fpiesik/ElektroCaster/docs/ext_ressources/circuits/piezoPreamps/Pokemon Ausmalbilder Kostenlos Malvorlagen Windowcolor zum Drucken-Dateien/ads_data_003/1356973211970626245.png

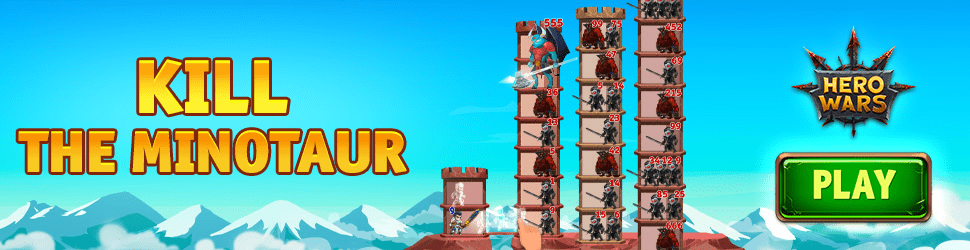
docs/ext_ressources/circuits/piezoPreamps/Pokemon Ausmalbilder Kostenlos Malvorlagen Windowcolor zum Drucken-Dateien/ads_data_003/1356973211970626245.png
