fpiesik/ElektroCaster/docs/UserInterface/DSC01511.JPG

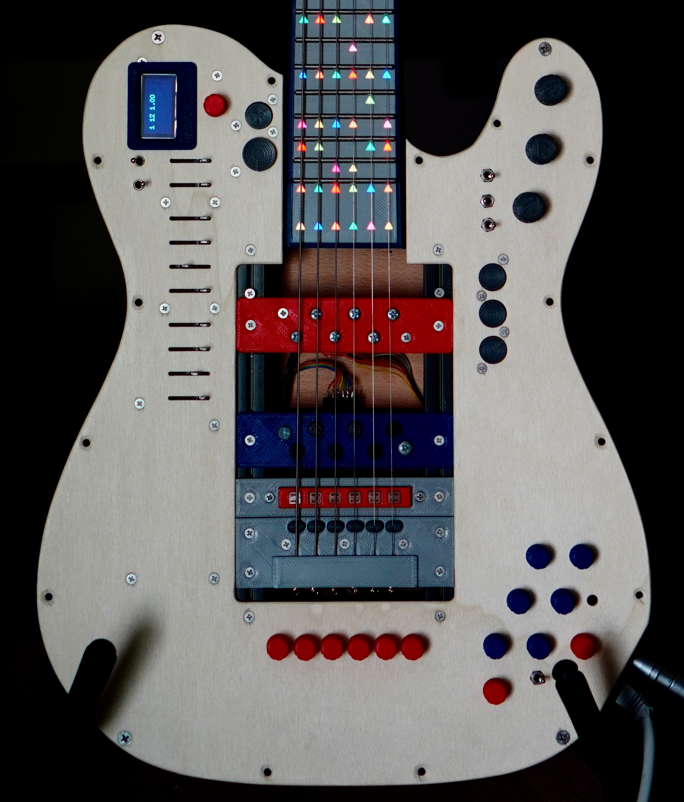
docs/UserInterface/DSC01511.JPG
