fpiesik/ElektroCaster/docs/ext_ressources/circuits/gk3.png

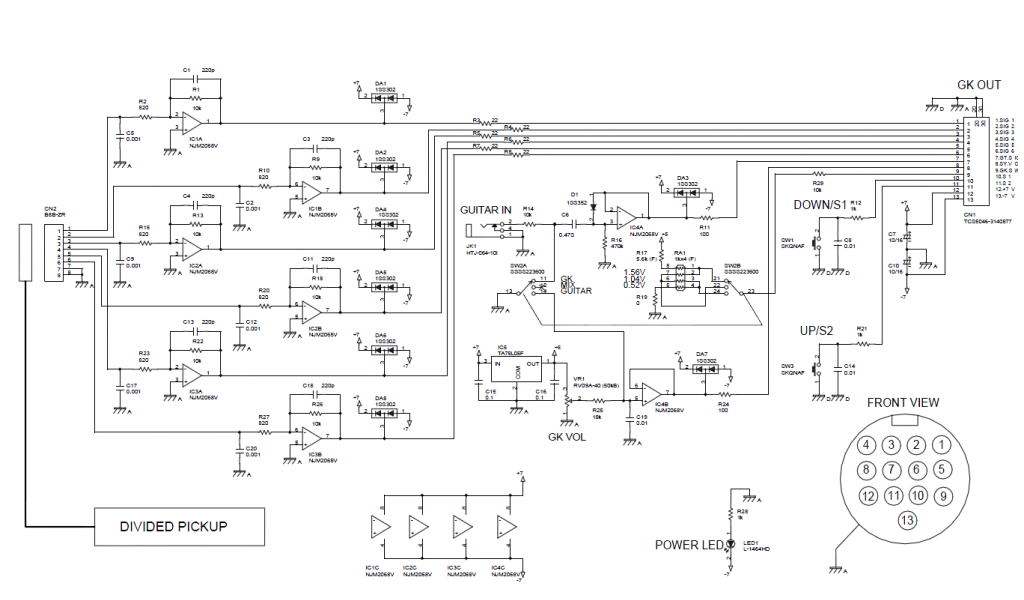
docs/ext_ressources/circuits/gk3.png
