fpiesik/ElektroCaster/docs/ext_ressources/circuits/gkCablePin.jpg

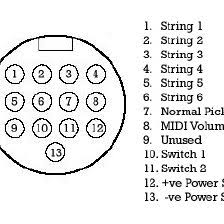
docs/ext_ressources/circuits/gkCablePin.jpg
