fpiesik/ElektroCaster/docs/ext_ressources/circuits/jfet-preamp.gif

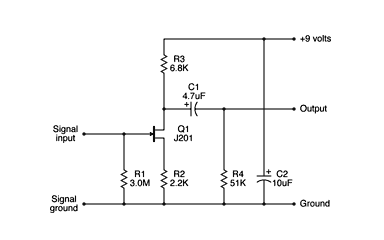
docs/ext_ressources/circuits/jfet-preamp.gif
