fpiesik/ElektroCaster/docs/ext_ressources/circuits/piezoPreamps/Pokemon Ausmalbilder Kostenlos Malvorlagen Windowcolor zum Drucken-Dateien/Ausmalbilder-Pokemon-Amphizel-300x236.jpg

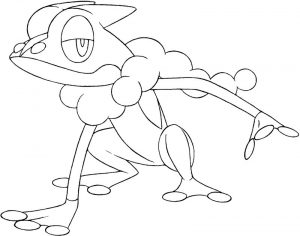
docs/ext_ressources/circuits/piezoPreamps/Pokemon Ausmalbilder Kostenlos Malvorlagen Windowcolor zum Drucken-Dateien/Ausmalbilder-Pokemon-Amphizel-300x236.jpg
