fpiesik/ElektroCaster/docs/ext_ressources/circuits/piezoPreamps/Pokemon Ausmalbilder Kostenlos Malvorlagen Windowcolor zum Drucken-Dateien/Ausmalbilder-Pokemon-Arceus-300x281.jpg

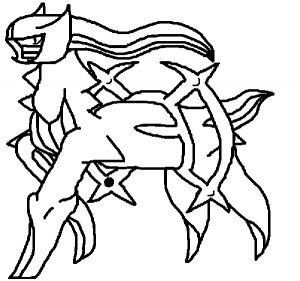
docs/ext_ressources/circuits/piezoPreamps/Pokemon Ausmalbilder Kostenlos Malvorlagen Windowcolor zum Drucken-Dateien/Ausmalbilder-Pokemon-Arceus-300x281.jpg
