fpiesik/ElektroCaster/docs/ext_ressources/circuits/piezoPreamps/Pokemon Ausmalbilder Kostenlos Malvorlagen Windowcolor zum Drucken-Dateien/Ausmalbilder-Pokemon-Ash.gif

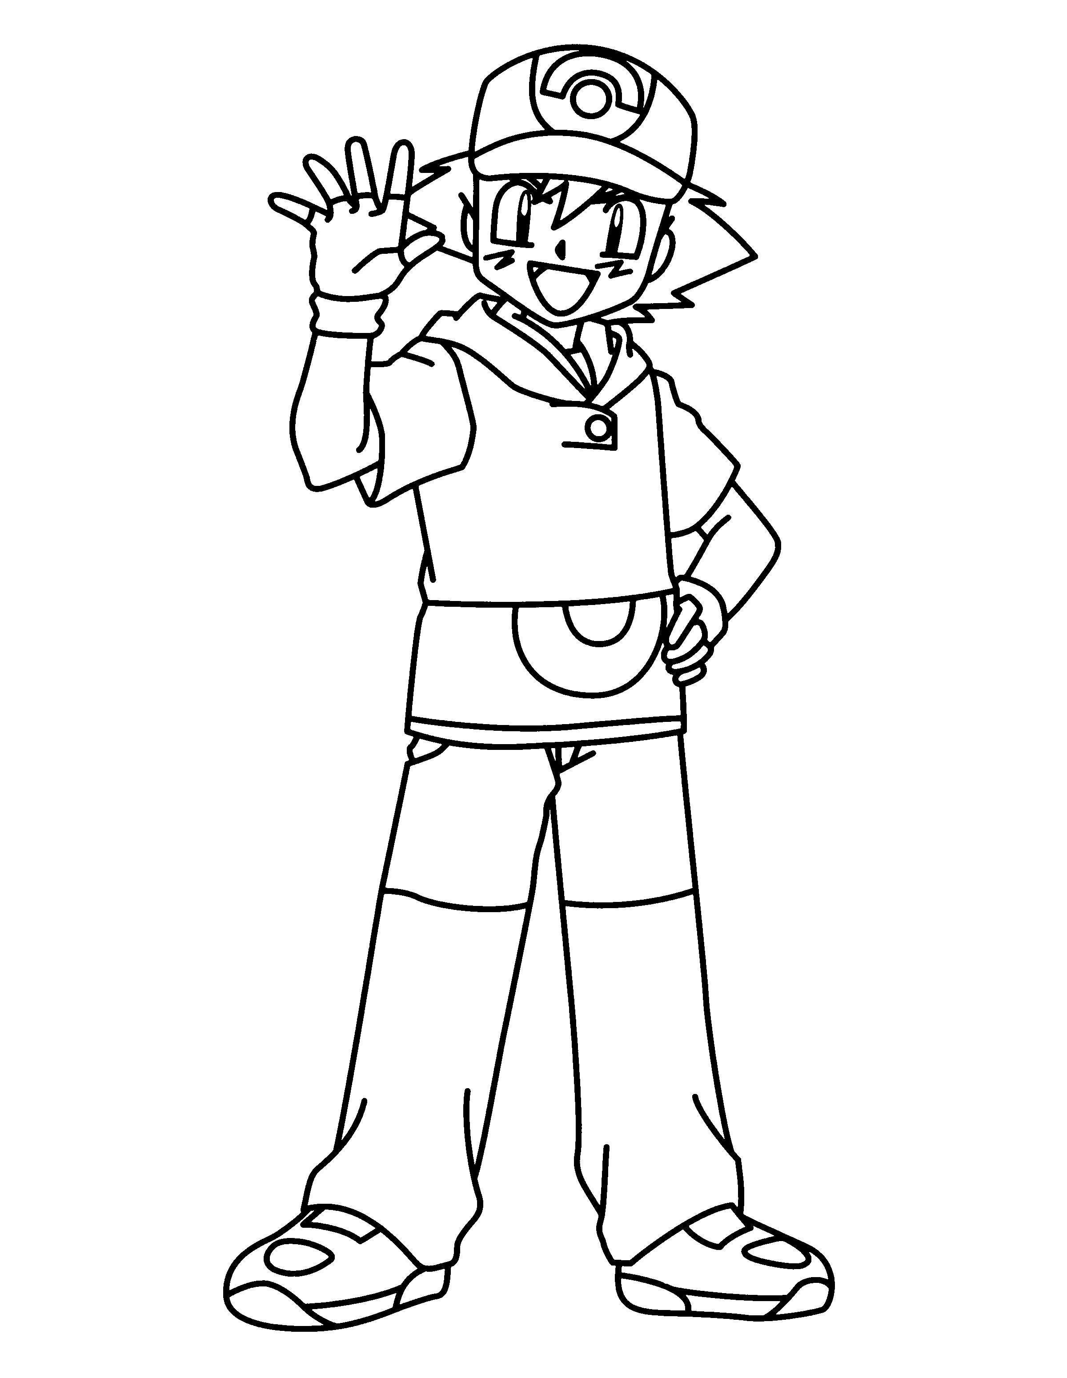
docs/ext_ressources/circuits/piezoPreamps/Pokemon Ausmalbilder Kostenlos Malvorlagen Windowcolor zum Drucken-Dateien/Ausmalbilder-Pokemon-Ash.gif
