fpiesik/ElektroCaster/docs/ext_ressources/circuits/piezoPreamps/Pokemon Ausmalbilder Kostenlos Malvorlagen Windowcolor zum Drucken-Dateien/Ausmalbilder-Pokemon-Ball.gif

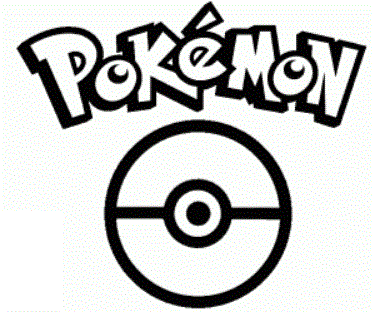
docs/ext_ressources/circuits/piezoPreamps/Pokemon Ausmalbilder Kostenlos Malvorlagen Windowcolor zum Drucken-Dateien/Ausmalbilder-Pokemon-Ball.gif
