fpiesik/ElektroCaster/docs/ext_ressources/circuits/piezoPreamps/prePiez.png

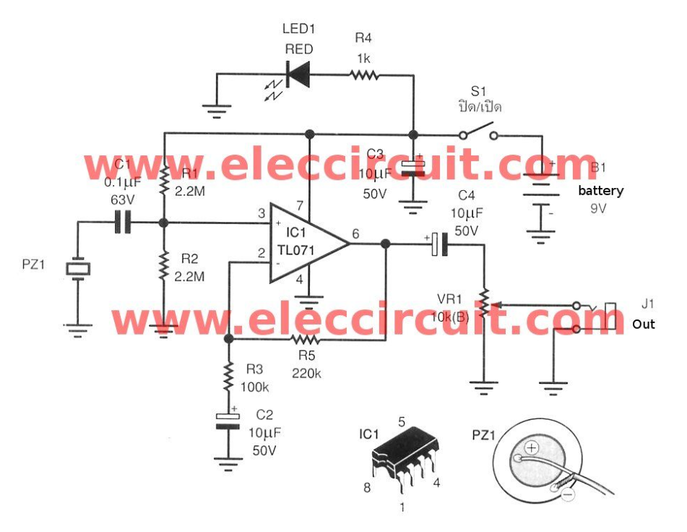
docs/ext_ressources/circuits/piezoPreamps/prePiez.png
