fpiesik/ElektroCaster/docs/ext_ressources/circuits/piezoPreamps/stack.png

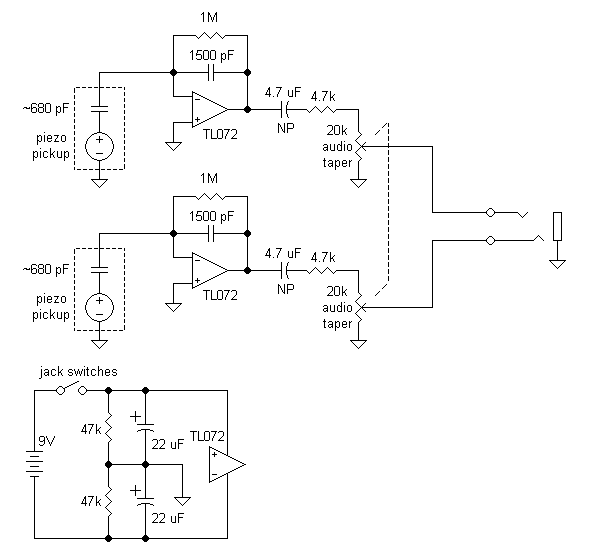
docs/ext_ressources/circuits/piezoPreamps/stack.png
