fpiesik/ElektroCaster/docs/ext_ressources/circuits/symmetricPower.jpg

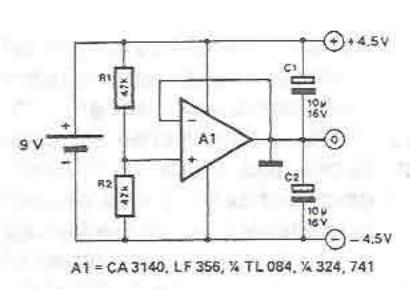
docs/ext_ressources/circuits/symmetricPower.jpg
