fpiesik/ElektroCaster/docs/ext_ressources/circuits/symmetricPower.png

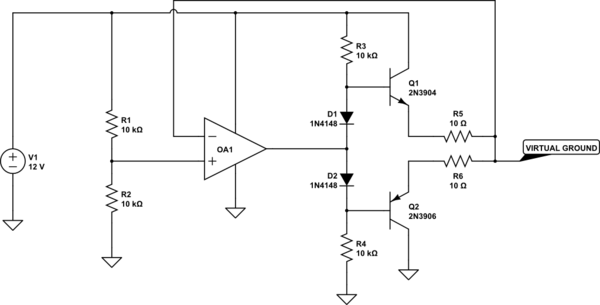
docs/ext_ressources/circuits/symmetricPower.png
