fpiesik/ElektroCaster/docs/UserInterface/PICT_20200703_101951.JPG

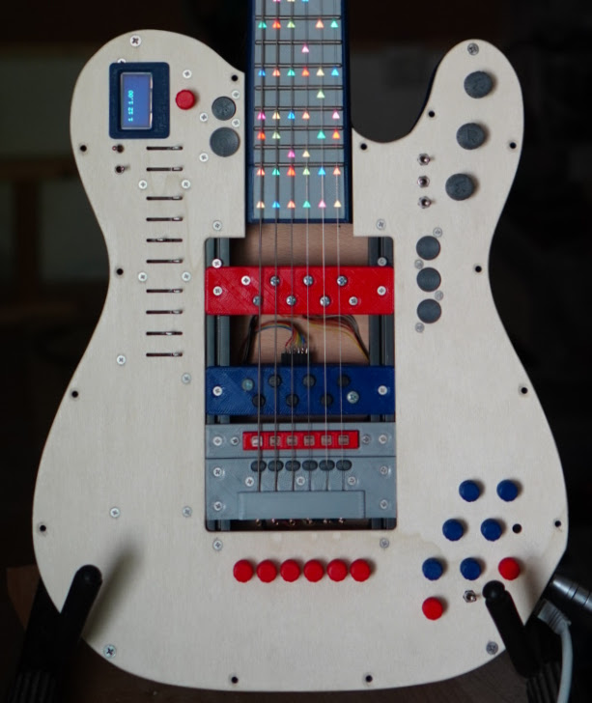
docs/UserInterface/PICT_20200703_101951.JPG
