fpiesik/ElektroCaster/mechanics/fretboard/fretConnect.stl

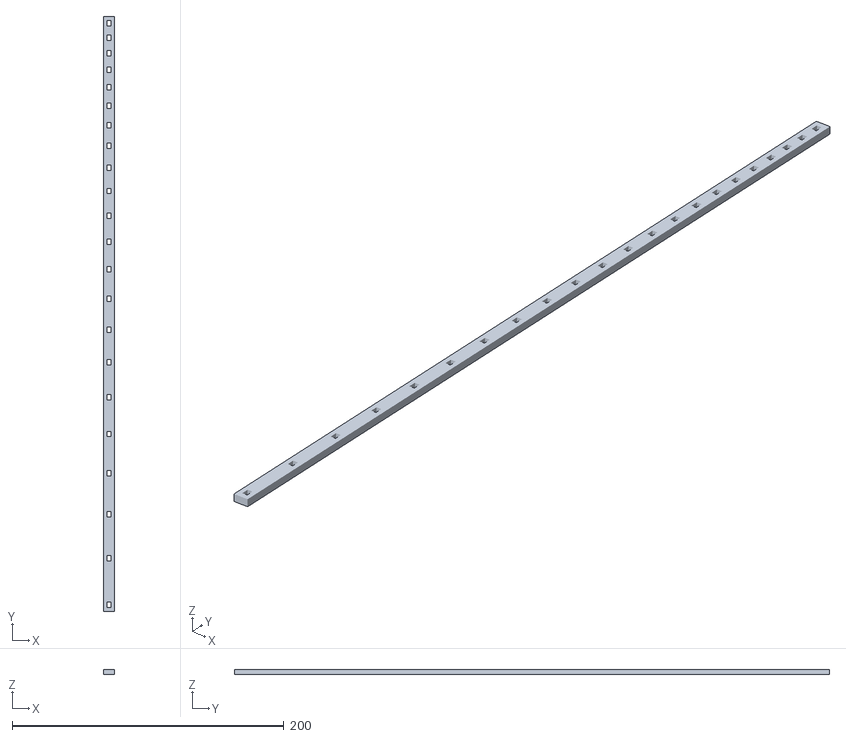
[picture p50: CAD file, 2022-02-02]
mechanics/fretboard/fretConnect.stl
8.00 x 437.8 x 4.00
