fpiesik/ElektroCaster/mechanics/knobs/knobs_joy.stl

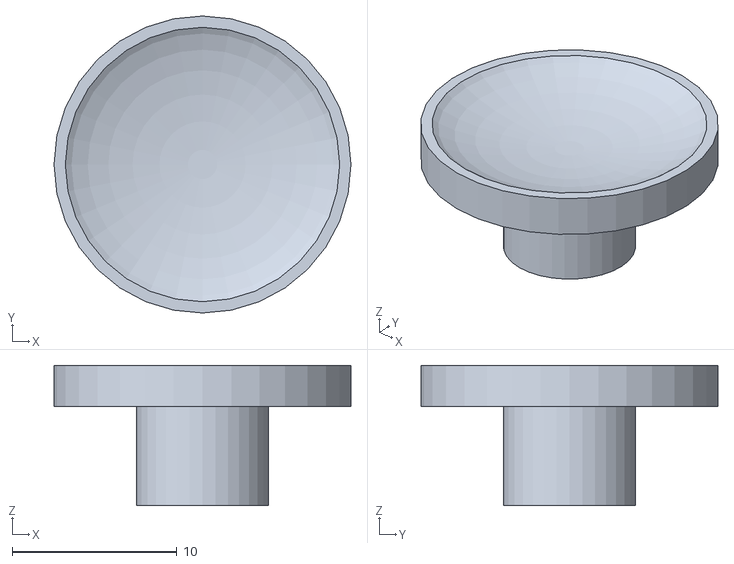
[picture p52: CAD file, 2020-10-20]
mechanics/knobs/knobs_joy.stl
18.0 x 18.0 x 8.50
