fpiesik/ElektroCaster/mechanics/neck/neck-over+side.stl

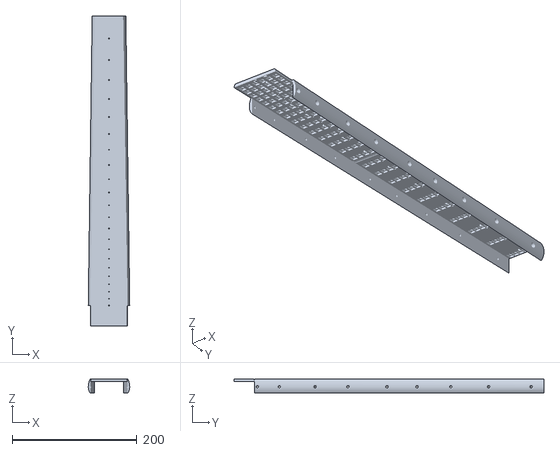
[picture p53: CAD file, 2022-02-02]
mechanics/neck/neck-over+side.stl
66.5 x 496.7 x 23.1
