fpiesik/ElektroCaster/mechanics/pickup(HB)/hexPickup-B.stl

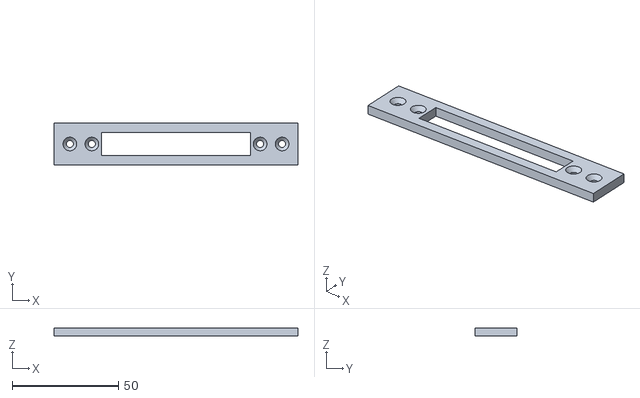
[picture p54: CAD file, 2020-10-20]
mechanics/pickup(HB)/hexPickup-B.stl
115.0 x 20.0 x 4.00
