fpiesik/ElektroCaster/mechanics/skeleton/slotBody2BackMntscad.stl

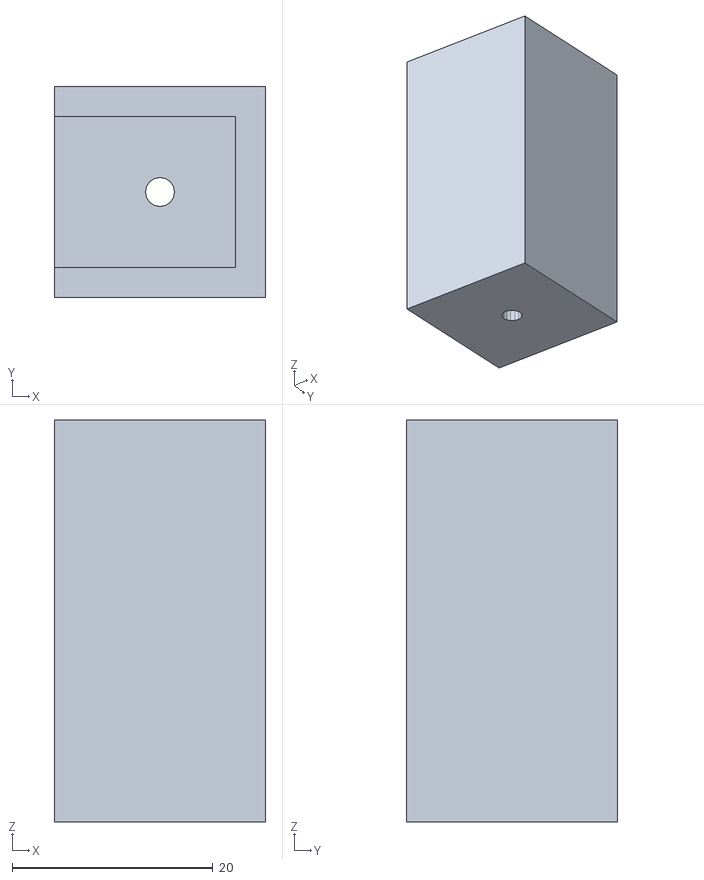
[picture p55: CAD file, 2020-10-20]
mechanics/skeleton/slotBody2BackMntscad.stl
21.0 x 21.0 x 40.0
