fpiesik/ElektroCaster/mechanics/body/bodyCont.stl

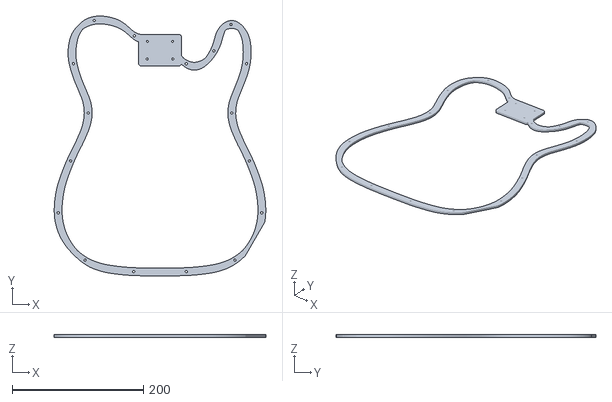
[picture p56: CAD file, 2020-10-20]
mechanics/body/bodyCont.stl
322.0 x 395.7 x 4.00
