fpiesik/ElektroCaster/mechanics/bridge/bridge-B (piezo).stl

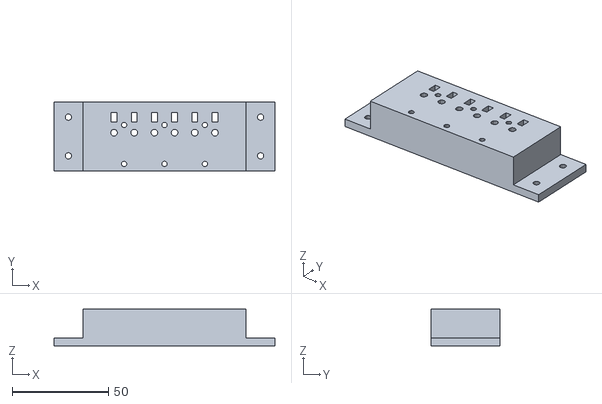
[picture p57: CAD file, 2022-02-02]
mechanics/bridge/bridge-B (piezo).stl
115.0 x 36.0 x 19.0
