fpiesik/ElektroCaster/mechanics/fretboard/fretboard.stl

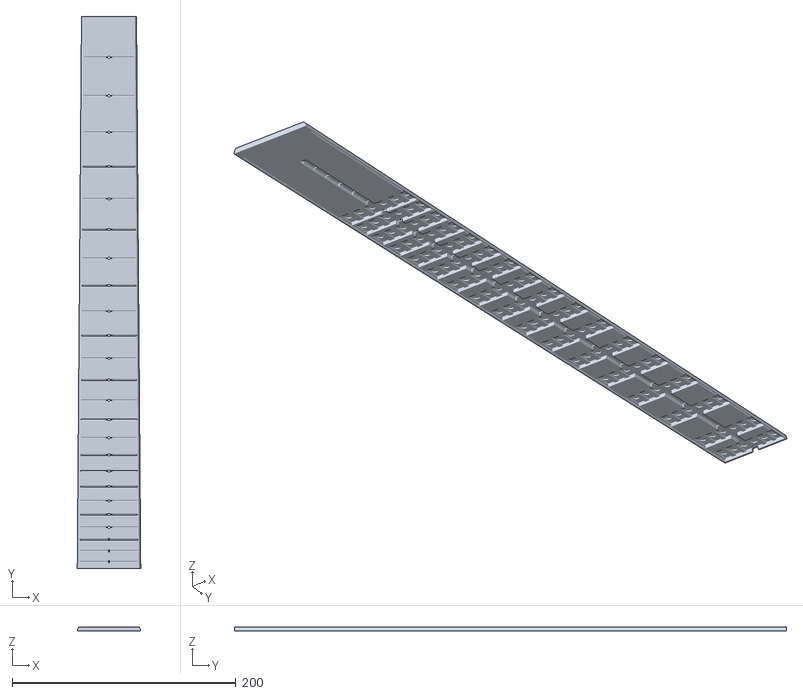
[picture p58: CAD file, 2020-10-20]
mechanics/fretboard/fretboard.stl
56.8 x 493.6 x 3.50
