fpiesik/ElektroCaster/mechanics/head/tuners.stl

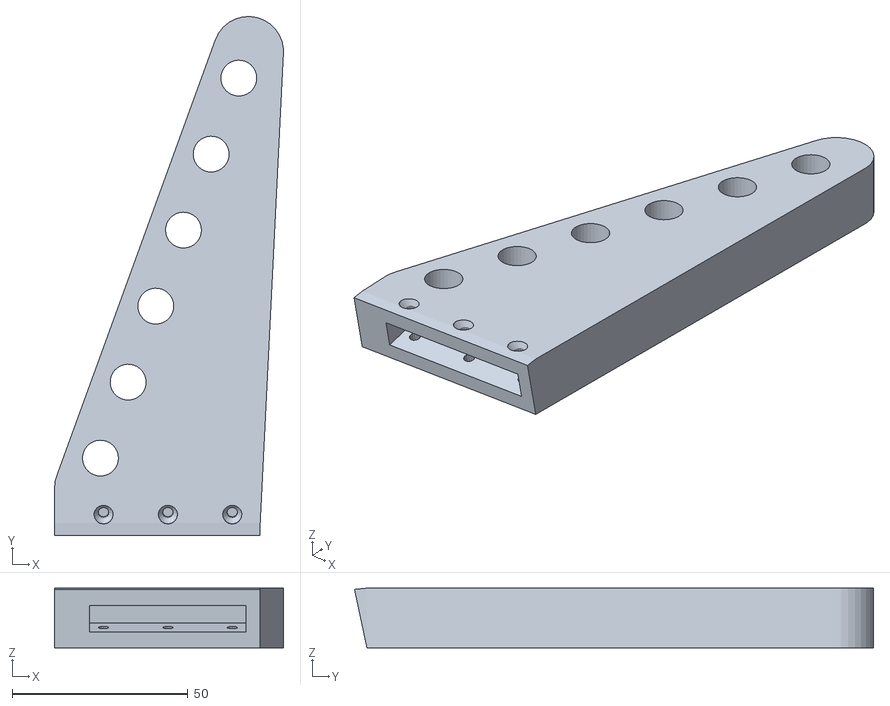
[picture p59: CAD file, 2020-10-20]
mechanics/head/tuners.stl
65.1 x 147.6 x 17.0
