fpiesik/ElektroCaster/mechanics/knobs/encKnob(ext).stl

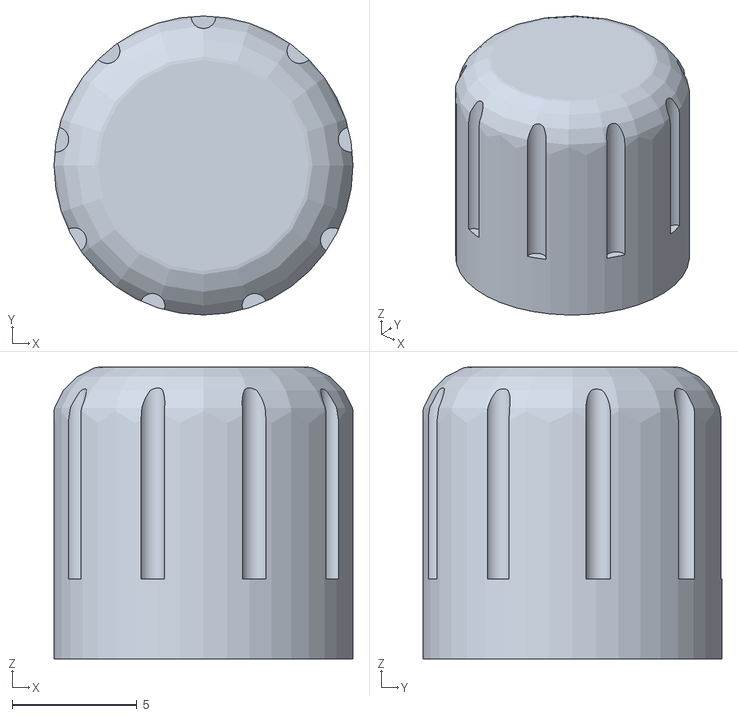
[picture p60: CAD file, 2020-10-20]
mechanics/knobs/encKnob(ext).stl
12.0 x 12.0 x 11.7
