fpiesik/ElektroCaster/mechanics/neck/neck-side.stl

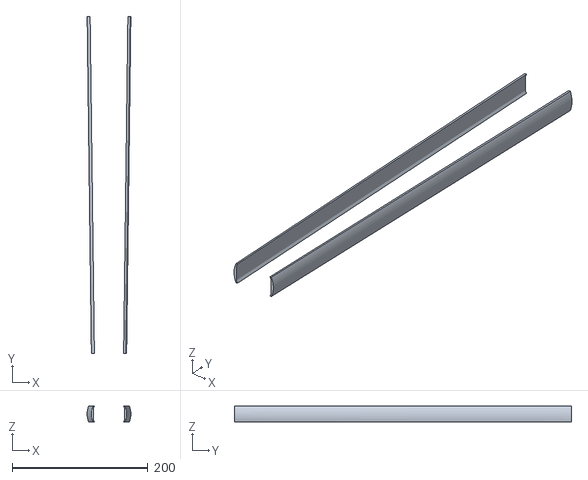
[picture p61: CAD file, 2020-10-20]
mechanics/neck/neck-side.stl
64.5 x 496.7 x 23.1
