fpiesik/ElektroCaster/mechanics/pickup(HB)/hexPickup-C.stl

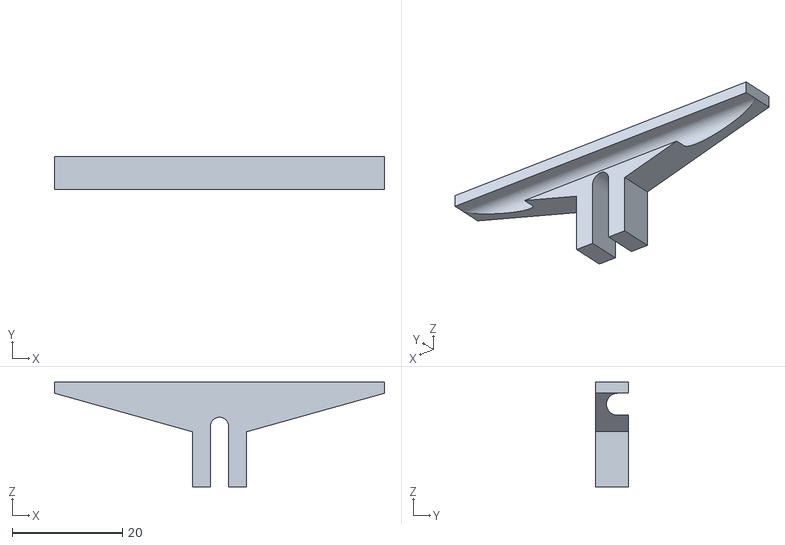
[picture p62: CAD file, 2020-10-20]
mechanics/pickup(HB)/hexPickup-C.stl
60.0 x 6.00 x 19.0
