fpiesik/ElektroCaster/docs/ext_ressources/nu_pickups/nu-master/cad_drawings/nu_multi/Nu_Multi_6_Routing_Template_Drawing.DXF

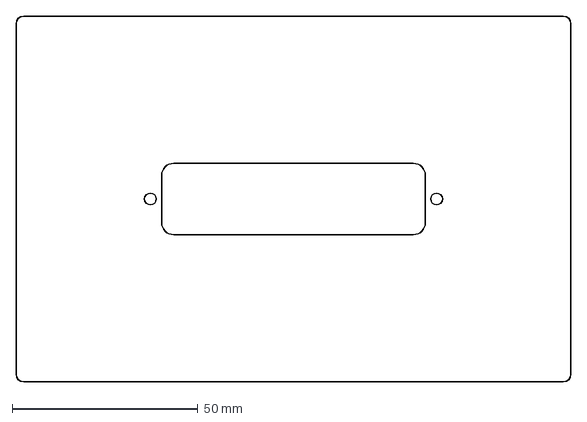
[picture p63: CAD file, 2022-02-02]
docs/ext_ressources/nu_pickups/nu-master/cad_drawings/nu_multi/Nu_Multi_6_Routing_Template_Drawing.DXF
149.2 x 98.4 mm
