fpiesik/ElektroCaster/mechanics/body/bodyConFilled.dxf

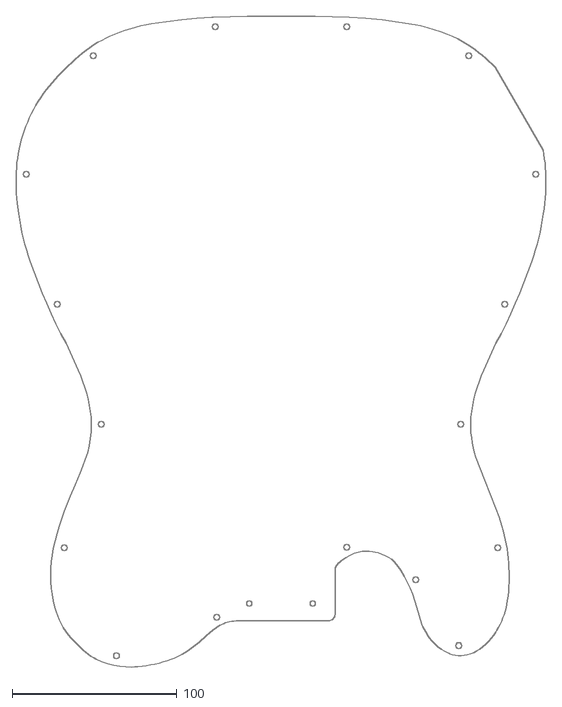
[picture p64: CAD file, 2020-10-20]
mechanics/body/bodyConFilled.dxf
322.0 x 395.7
