fpiesik/ElektroCaster/mechanics/bridge/bridge-A (piezo).stl

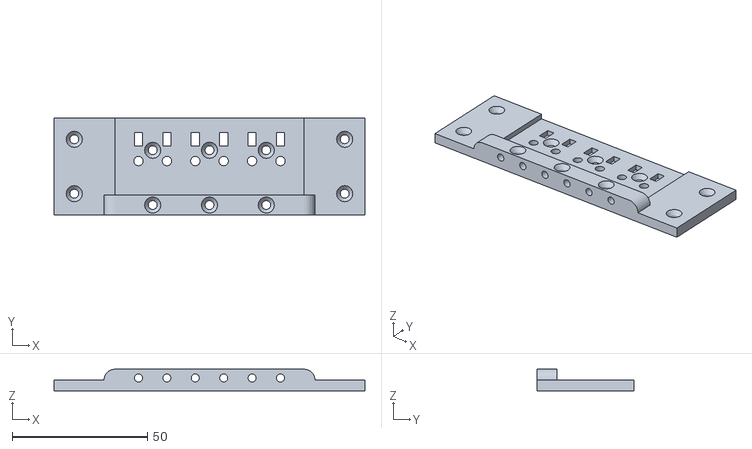
[picture p65: CAD file, 2022-02-02]
mechanics/bridge/bridge-A (piezo).stl
115.0 x 36.0 x 8.00
