fpiesik/ElektroCaster/mechanics/fretboard/overlay.stl

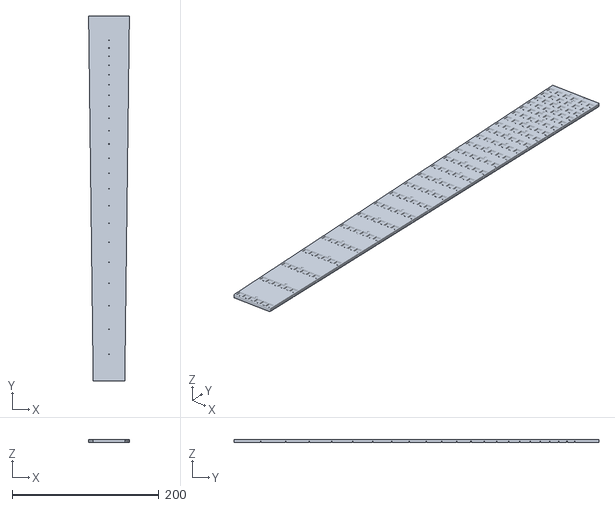
[picture p66: CAD file, 2020-10-20]
mechanics/fretboard/overlay.stl
55.4 x 496.7 x 3.50
