fpiesik/ElektroCaster/mechanics/kickup_mEbow/mcMag.stl

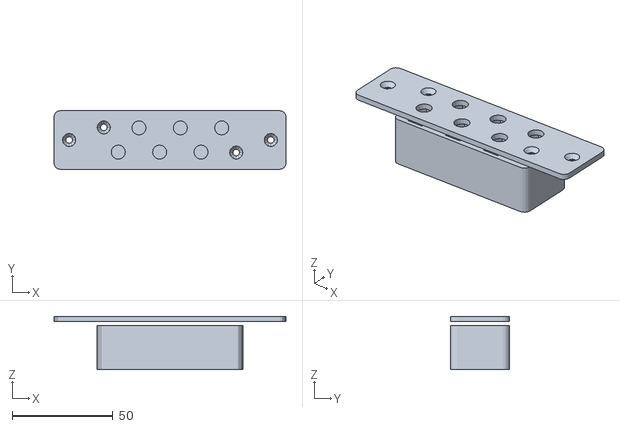
[picture p67: CAD file, 2020-10-20]
mechanics/kickup_mEbow/mcMag.stl
115.0 x 29.0 x 26.3
