fpiesik/ElektroCaster/mechanics/knobs/knobs_button.stl

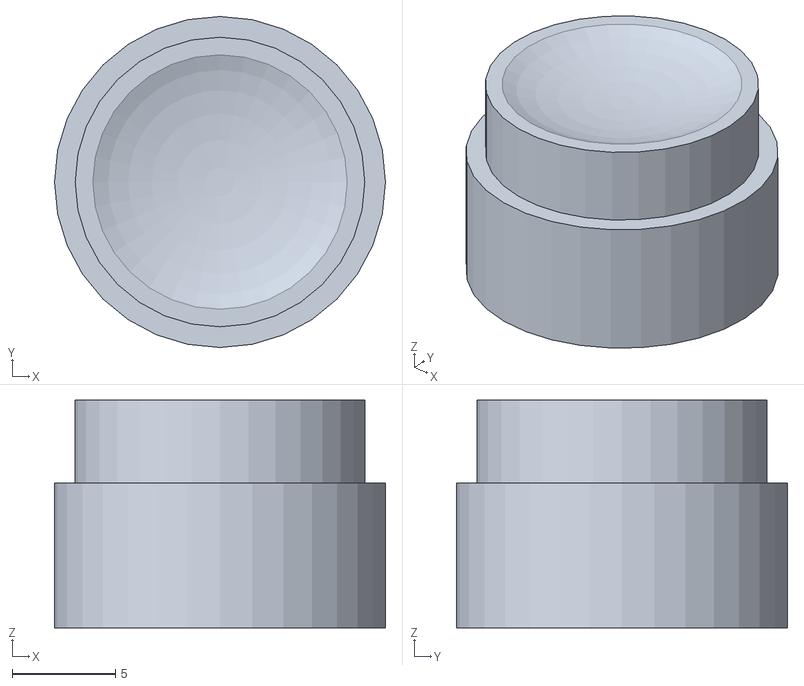
[picture p68: CAD file, 2020-10-20]
mechanics/knobs/knobs_button.stl
16.0 x 16.0 x 11.0
