fpiesik/ElektroCaster/mechanics/neck/neck-endB.stl

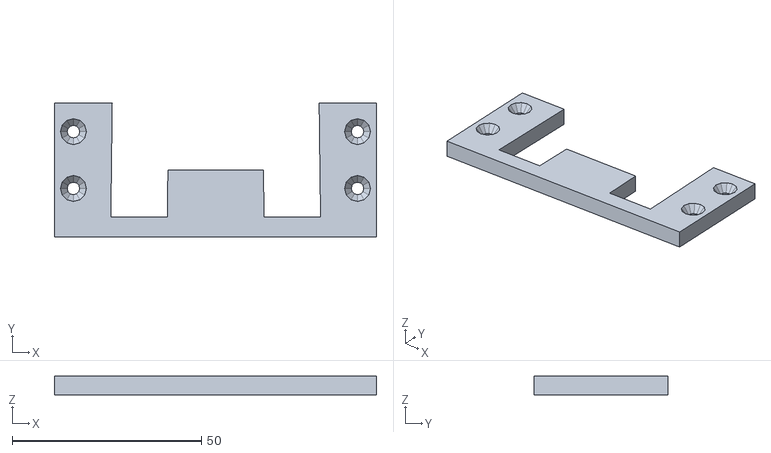
[picture p69: CAD file, 2020-10-20]
mechanics/neck/neck-endB.stl
85.0 x 35.2 x 5.00
