fpiesik/ElektroCaster/mechanics/pickup(HB)/hexPickup-A.stl

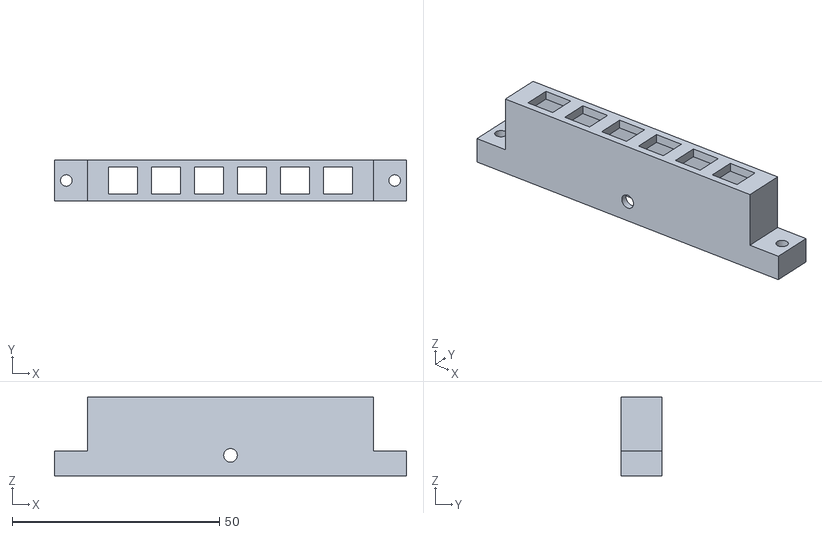
[picture p70: CAD file, 2020-10-20]
mechanics/pickup(HB)/hexPickup-A.stl
85.0 x 10.0 x 19.0
