fpiesik/ElektroCaster/mechanics/body/centerLine.dxf

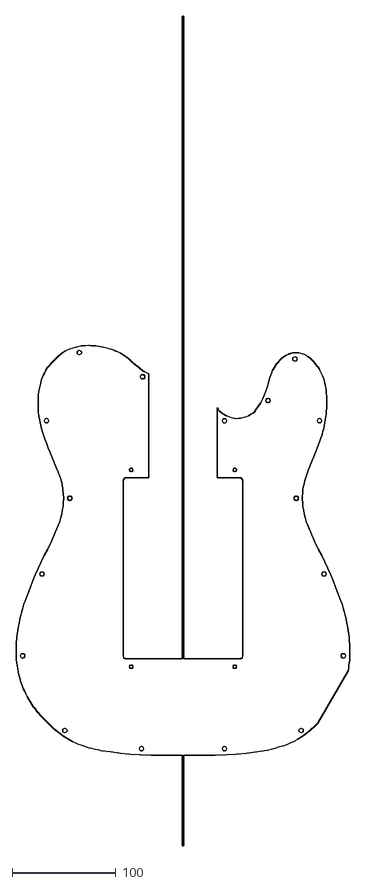
[picture p71: CAD file, 2020-10-20]
mechanics/body/centerLine.dxf
322.0 x 800.0
