fpiesik/ElektroCaster/mechanics/bridge/bridge-A.stl

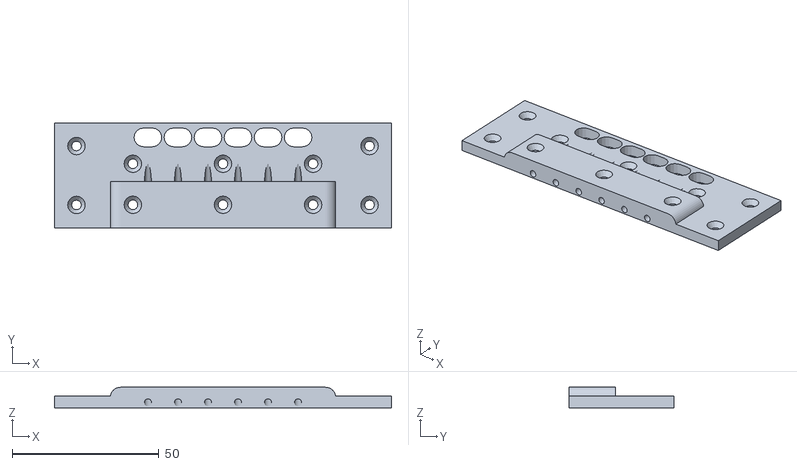
[picture p72: CAD file, 2021-02-15]
mechanics/bridge/bridge-A.stl
115.0 x 36.0 x 7.00
