fpiesik/ElektroCaster/mechanics/fretboard/contour.dxf

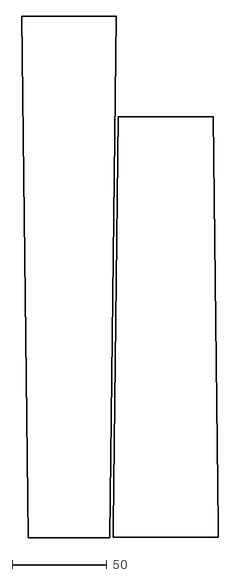
[picture p73: CAD file, 2020-10-20]
mechanics/fretboard/contour.dxf
103.7 x 275.0
