fpiesik/ElektroCaster/mechanics/kickup_mEbow/mcMag-top.stl

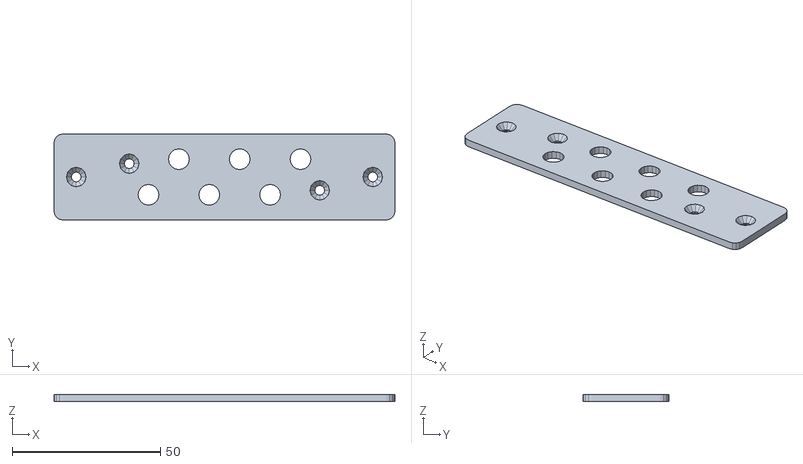
[picture p74: CAD file, 2020-10-20]
mechanics/kickup_mEbow/mcMag-top.stl
115.0 x 29.0 x 2.50
