fpiesik/ElektroCaster/mechanics/body/bodyTop(noKnobs).dxf

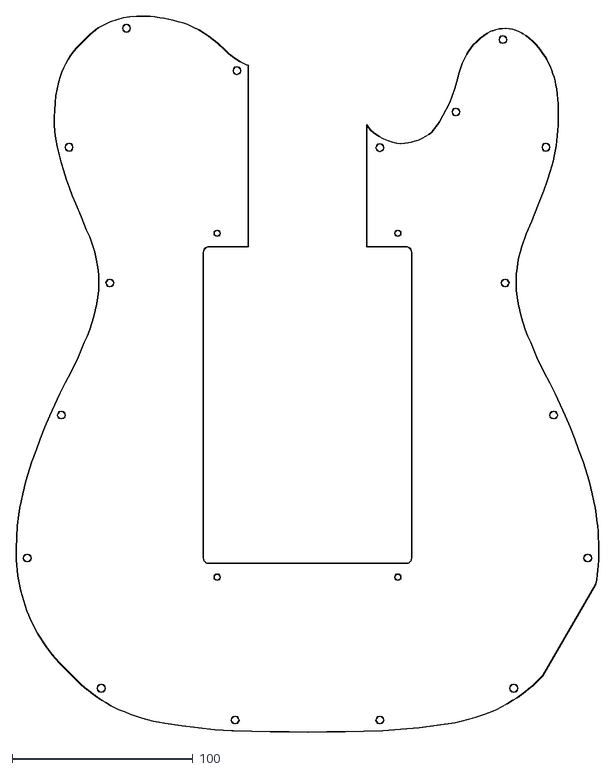
[picture p75: CAD file, 2020-10-20]
mechanics/body/bodyTop(noKnobs).dxf
322.0 x 395.7
