fpiesik/ElektroCaster/mechanics/bridge/bridge-C.stl

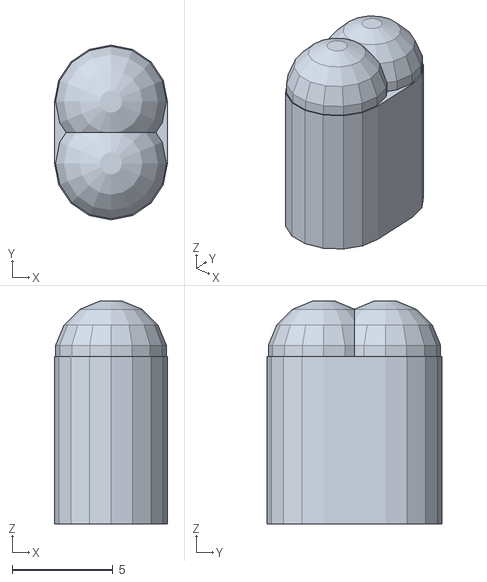
[picture p76: CAD file, 2021-02-15]
mechanics/bridge/bridge-C.stl
5.60 x 8.65 x 11.0
