fpiesik/ElektroCaster/mechanics/fretboard/traces.dxf

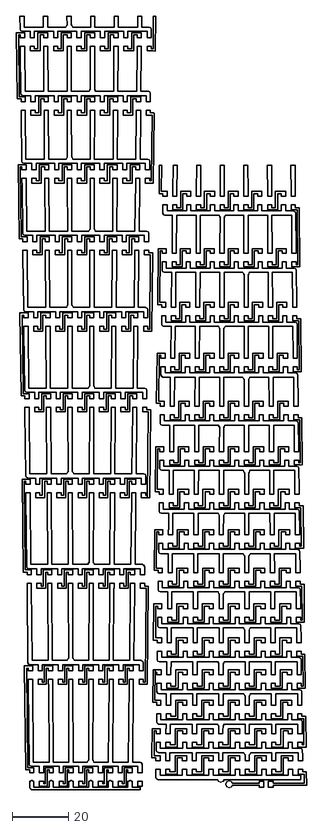
[picture p77: CAD file, 2020-10-20]
mechanics/fretboard/traces.dxf
103.2 x 275.0
