fpiesik/ElektroCaster/mechanics/kickup_mEbow/kickup.stl

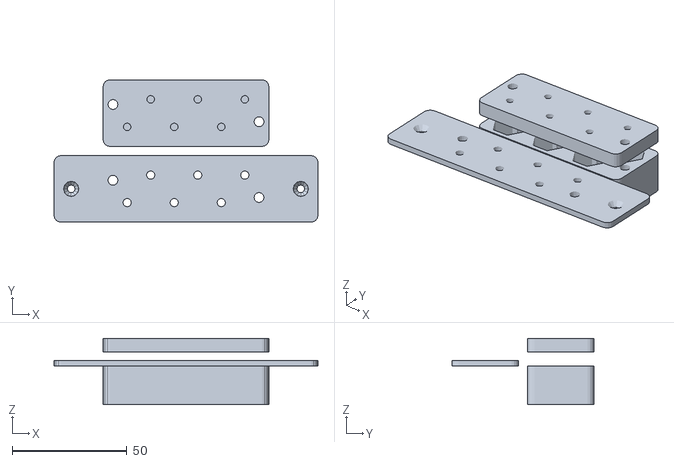
[picture p78: CAD file, 2020-10-20]
mechanics/kickup_mEbow/kickup.stl
115.0 x 62.0 x 28.8
