fpiesik/ElektroCaster/mechanics/neck/neck-mntSide.stl

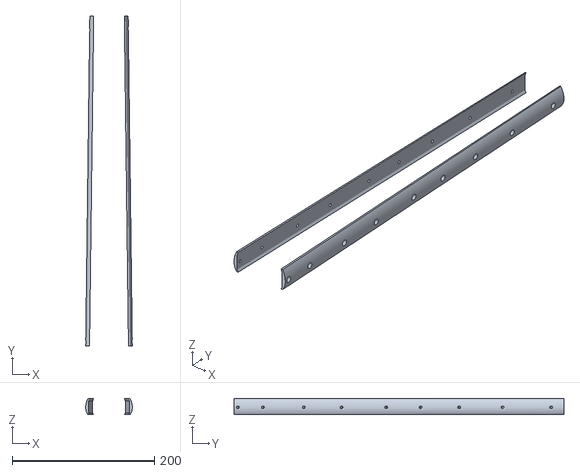
[picture p79: CAD file, 2020-10-20]
mechanics/neck/neck-mntSide.stl
65.7 x 464.0 x 23.1
