fpiesik/ElektroCaster/mechanics/body/body.stl

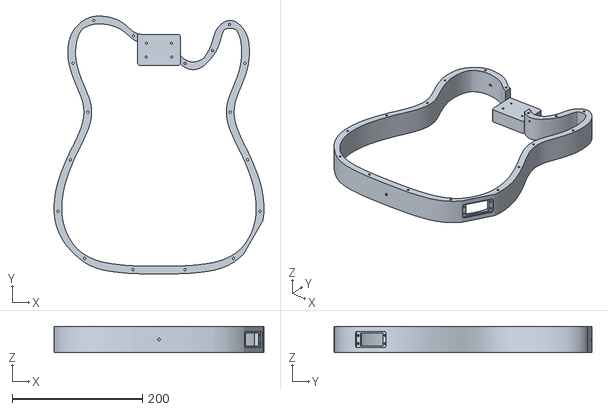
[picture p80: CAD file, 2020-10-20]
mechanics/body/body.stl
322.0 x 395.7 x 40.0
