fpiesik/ElektroCaster/mechanics/bridge/bridge-B.stl

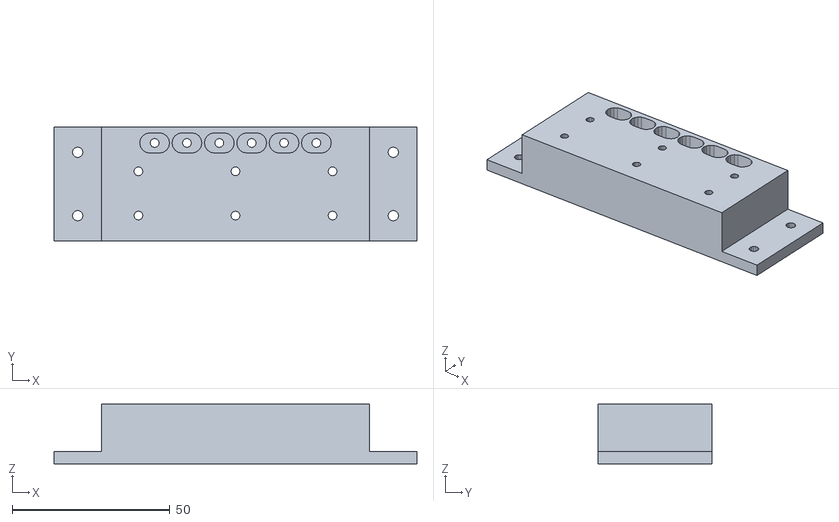
[picture p81: CAD file, 2021-02-15]
mechanics/bridge/bridge-B.stl
115.0 x 36.0 x 19.0
