fpiesik/ElektroCaster/mechanics/fretboard/ledStripe-drill.dxf

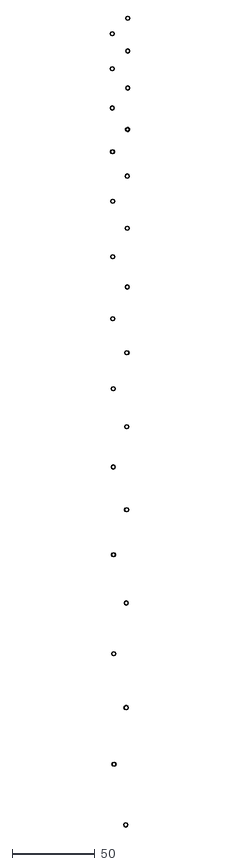
[picture p82: CAD file, 2020-10-20]
mechanics/fretboard/ledStripe-drill.dxf
11.9 x 490.0
