fpiesik/ElektroCaster/mechanics/neck/neck-over.stl

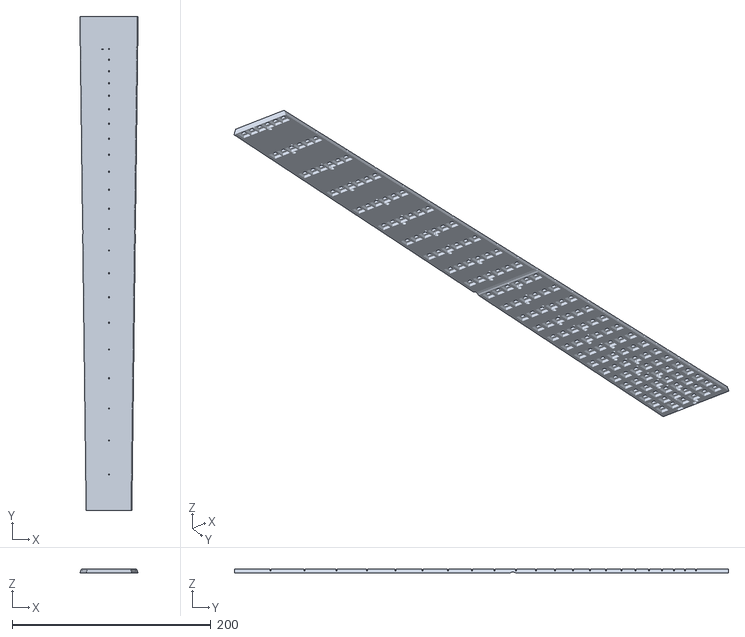
[picture p83: CAD file, 2020-10-20]
mechanics/neck/neck-over.stl
58.5 x 496.7 x 4.00
