fpiesik/ElektroCaster/mechanics/body/bodyContFilled2.stl

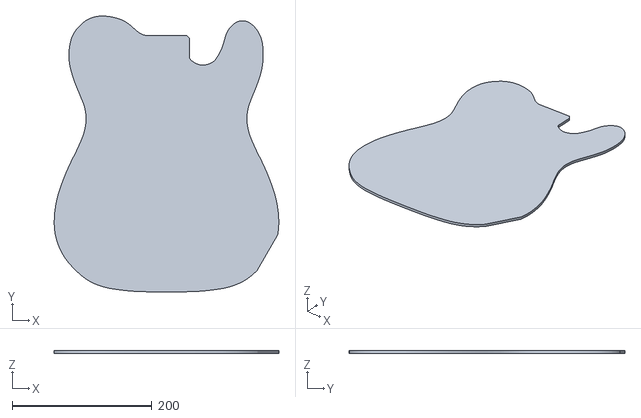
[picture p84: CAD file, 2020-10-20]
mechanics/body/bodyContFilled2.stl
322.0 x 395.7 x 4.00
