fpiesik/ElektroCaster/mechanics/fretboard/holes.dxf

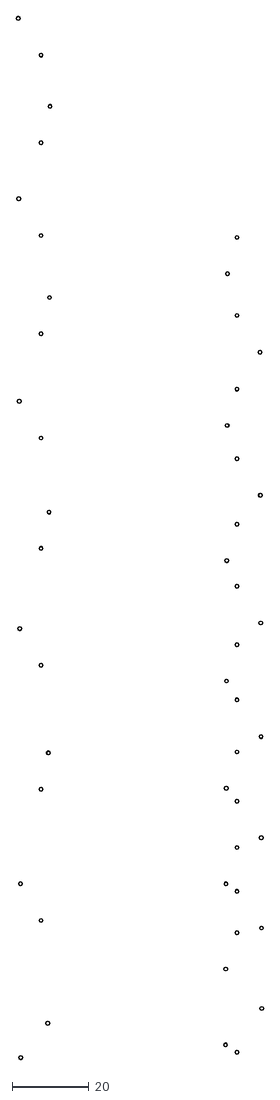
[picture p85: CAD file, 2020-10-20]
mechanics/fretboard/holes.dxf
64.4 x 271.5
