fpiesik/ElektroCaster/mechanics/neck/neck-sideB.stl

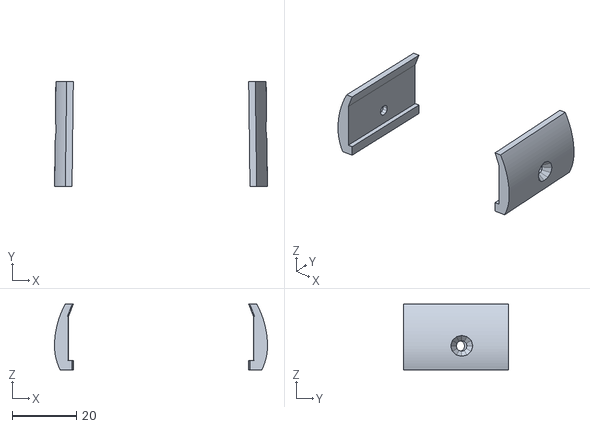
[picture p86: CAD file, 2020-10-20]
mechanics/neck/neck-sideB.stl
66.5 x 32.7 x 20.6
