fpiesik/ElektroCaster/mechanics/body/bodyContour.dxf

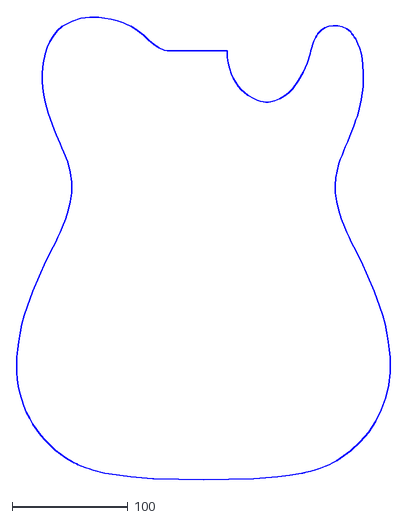
[picture p87: CAD file, 2019-02-02]
mechanics/body/bodyContour.dxf
323.4 x 400.7
