fpiesik/ElektroCaster/mechanics/fretboard/ledStripe.dxf

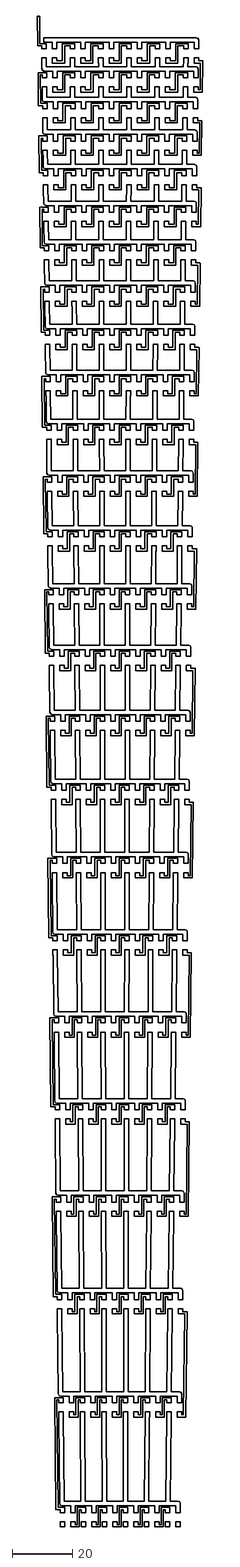
[picture p88: CAD file, 2020-10-20]
mechanics/fretboard/ledStripe.dxf
55.1 x 503.1
