fpiesik/ElektroCaster/mechanics/neck/neck-end.stl

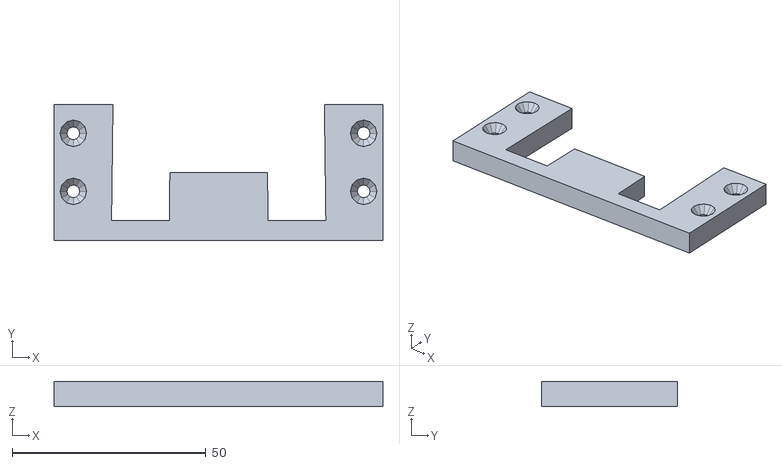
[picture p89: CAD file, 2020-10-20]
mechanics/neck/neck-end.stl
85.0 x 35.2 x 6.50
