fpiesik/ElektroCaster/mechanics/body/bodyTop.stl

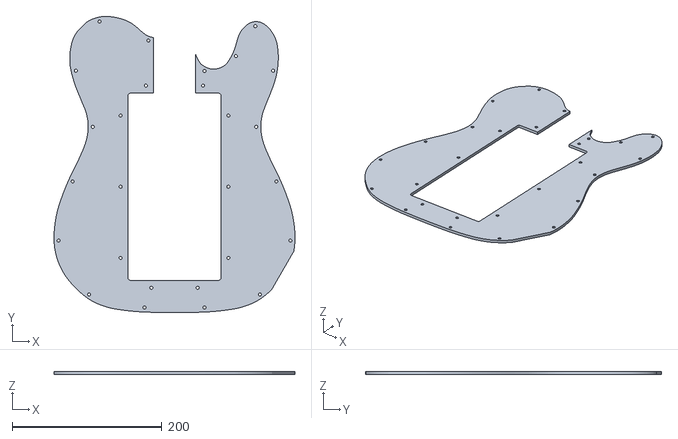
[picture p90: CAD file, 2019-02-02]
mechanics/body/bodyTop.stl
322.0 x 395.7 x 4.00
