fpiesik/ElektroCaster/mechanics/body/bodyContFilled.stl

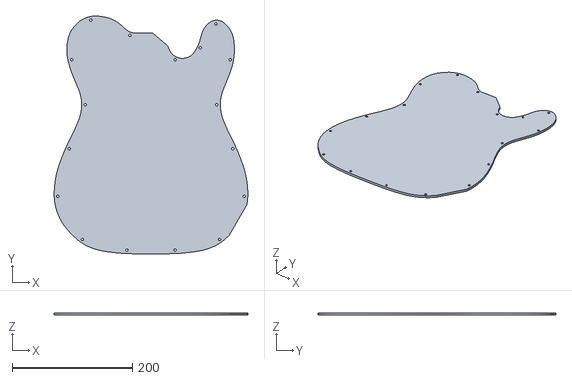
[picture p91: CAD file, 2019-02-02]
mechanics/body/bodyContFilled.stl
322.0 x 395.7 x 4.00
