fpiesik/ElektroCaster/electronics/hexPreamp(jfet)/case.scad

wO=40;
wthick=1;
wI=wO-wthick*2;

lO=90;
lI=lO-wthick*2;

h=20;


translate([0,0,h/2])cube([lO,wO,h],center=true);
