fpiesik/ElektroCaster/mechanics/body/inkbody.scad

// Module names are of the form poly_<inkscape-path-id>().
// As a result you can associate a polygon in this OpenSCAD program with the
//  corresponding SVG element in the Inkscape document by looking for 
//  the XML element with the attribute id="inkscape-path-id".

// Paths have their own variables so they can be imported and used 
//  in polygon(points) structures in other programs.
// The NN_points is the list of all polygon XY vertices. 
// There may be an NN_paths variable as well. If it exists then it 
//  defines the nested paths. Both must be used in the 
//  polygon(points, paths) variant of the command.

profile_scale = 25.4/90; //made in inkscape in mm

// helper functions to determine the X,Y dimensions of the profiles
function min_x(shape_points) = min([ for (x = shape_points) min(x[0])]);
function max_x(shape_points) = max([ for (x = shape_points) max(x[0])]);
function min_y(shape_points) = min([ for (x = shape_points) min(x[1])]);
function max_y(shape_points) = max([ for (x = shape_points) max(x[1])]);

height = 5;
width = 1.0;


path5353_0_points = [[290.911295,-521.752208],[300.775361,-534.505677],[309.902984,-547.742083],[318.278105,-561.429609],[325.884668,-575.536435],[332.706617,-590.030743],[338.727895,-604.880713],[343.932444,-620.054526],[348.304209,-635.520364],[354.002579,-655.936458],[360.678330,-676.060254],[363.301077,-682.612221],[366.363104,-688.966025],[369.853326,-695.099981],[373.760659,-700.992400],[378.552339,-706.731613],[383.900926,-711.822054],[389.740561,-716.249652],[396.005389,-720.000332],[402.629552,-723.060022],[409.547192,-725.414649],[416.692452,-727.050141],[423.999476,-727.952423],[431.402407,-728.107425],[438.835386,-727.501071],[446.232557,-726.119291],[453.528062,-723.948010],[460.656045,-720.973156],[467.550649,-717.180655],[474.146016,-712.556436],[480.376288,-707.086425],[484.929070,-701.778080],[489.164658,-696.225857],[493.073164,-690.443682],[496.644697,-684.445477],[500.639438,-676.880058],[504.274553,-669.153911],[507.545772,-661.279698],[510.448830,-653.270080],[512.979458,-645.137720],[515.133388,-636.895279],[516.906355,-628.555417],[518.294089,-620.130798],[519.724523,-608.899201],[520.850473,-597.647914],[521.672387,-586.382908],[522.190714,-575.110157],[522.405902,-563.835635],[522.318400,-552.565314],[521.928657,-541.305167],[521.237121,-530.061167],[520.244240,-518.839288],[518.950463,-507.645503],[517.356239,-496.485785],[515.462017,-485.366106],[513.268244,-474.292440],[510.775370,-463.270761],[507.983843,-452.307040],[504.894111,-441.407252]];
path5353_1_points = [[463.819263,-332.460017],[452.676031,-304.940580],[442.610874,-277.016939]];
path5353_2_points = [[447.012506,686.324879],[455.979492,680.365260],[464.730909,674.163900],[473.263284,667.726789],[481.573146,661.059921],[489.657020,654.169289],[497.511435,647.060884],[505.132917,639.740700],[512.517994,632.214728],[519.663193,624.488961],[526.565040,616.569392],[533.220064,608.462013],[539.624792,600.172816],[545.775749,591.707795],[551.669465,583.072940],[557.302465,574.274246],[562.671278,565.317703],[567.772430,556.209306],[572.602448,546.955045],[577.157860,537.560915],[581.435193,528.032906],[585.430974,518.377012],[589.141731,508.599224],[592.563989,498.705537],[595.694278,488.701941],[598.529123,478.594429],[601.065052,468.388994],[603.298592,458.091629],[605.226271,447.708325],[606.844615,437.245075],[608.150152,426.707872],[609.139408,416.102708],[609.808912,405.435576]];
path5353_3_points = [[442.614947,-277.016939],[439.226475,-265.396530],[436.367518,-253.656044],[434.040351,-241.813180],[432.247249,-229.885640],[430.990487,-217.891123],[430.272341,-205.847329],[430.095087,-193.771958],[430.460999,-181.682709]];
path5353_4_points = [[430.460999,-181.684023],[432.269928,-167.109492],[434.683009,-152.640034],[437.695241,-138.293720],[441.301623,-124.088619],[445.497157,-110.042802],[450.276840,-96.174337],[455.635674,-82.501296],[461.568658,-69.041747]];
path5353_5_points = [[461.568658,-69.041747],[475.638714,-36.643527],[490.719059,-4.692912]];
path5353_6_points = [[575.868423,190.747218],[566.973642,165.602070],[557.572761,140.646458],[547.668989,115.887775],[537.265535,91.333416],[526.365607,66.990774],[514.972413,42.867242],[503.089161,18.970216],[490.719059,-4.692912]];
path5353_7_points = [[604.079539,305.735709],[601.887231,291.068939],[599.310115,276.471243],[596.350011,261.949971],[593.008741,247.512472],[589.288126,233.166097],[585.189987,218.918196],[580.716146,204.776120],[575.868423,190.747218]];
path5353_8_points = [[609.808912,405.435576],[610.153109,392.932293],[610.193740,380.429866],[609.931107,367.933696],[609.365511,355.449183],[608.497255,342.981727],[607.326639,330.536729],[605.853967,318.119589],[604.079539,305.735709]];
path5353_9_points = [[334.803996,731.830129],[350.719196,727.624021],[366.474044,722.879552],[382.054599,717.601194],[397.446920,711.793416]];
path5353_10_points = [[163.557970,752.460102],[203.253864,749.737554],[242.841896,745.850708],[282.295883,740.802557],[321.589642,734.596092]];
path5353_11_points = [[-162.047715,752.511336],[-121.354457,753.704430],[-80.654675,754.554836],[-39.950567,755.062564],[0.755669,755.227625],[41.461838,755.050030],[82.165743,754.529790],[122.865186,753.666915],[163.557970,752.461416]];
path5353_12_points = [[-310.156338,736.525501],[-274.079401,741.952427],[-237.873087,746.404607],[-201.557433,749.879504],[-165.152478,752.374581]];
path5353_13_points = [[-410.189618,706.525935],[-397.849406,711.636849],[-385.371848,716.403070],[-372.764285,720.821985],[-360.034056,724.890984]];
path5353_14_points = [[-609.847492,404.626609],[-609.145077,416.045730],[-608.076903,427.390767],[-606.647415,438.654551],[-604.861060,449.829913],[-602.722286,460.909684],[-600.235538,471.886696],[-597.405265,482.753781],[-594.235913,493.503770],[-590.731929,504.129495],[-586.897760,514.623787],[-582.737852,524.979477],[-578.256653,535.189397],[-573.458610,545.246379],[-568.348169,555.143254],[-562.929778,564.872853],[-557.207883,574.428008],[-551.186931,583.801551],[-544.871370,592.986312],[-538.265645,601.975125],[-531.374205,610.760818],[-524.201496,619.336226],[-516.751964,627.694178],[-509.030057,635.827507],[-501.040222,643.729043],[-492.786906,651.391619],[-484.274555,658.808065],[-475.507616,665.971214],[-466.490537,672.873897],[-457.227764,679.508945],[-447.723744,685.869190],[-437.982924,691.947463],[-428.009751,697.736596]];
path5353_15_points = [[-604.079890,305.736365],[-607.308318,330.335473],[-609.347027,355.045028],[-610.193740,379.822813],[-609.846178,404.626609]];
path5353_16_points = [[-575.873897,190.747744],[-580.720662,204.776649],[-585.193682,218.918727],[-589.291113,233.166628],[-593.011111,247.513002],[-596.351833,261.950500],[-599.311432,276.471771],[-601.888066,291.069465],[-604.079890,305.736234]];
path5353_17_points = [[-490.719541,-4.692387],[-503.090962,18.970310],[-514.975393,42.867027],[-526.369597,66.990372],[-537.270337,91.332951],[-547.674374,115.887371],[-557.578471,140.646239],[-566.979392,165.602161],[-575.873897,190.747744]];
path5353_18_points = [[-490.719541,-4.692387],[-475.641003,-36.643000],[-461.572950,-69.041209]];
path5353_19_points = [[-461.574133,-69.041209],[-455.639842,-82.500381],[-450.280041,-96.173230],[-445.499722,-110.041623],[-441.303879,-124.087430],[-437.697508,-138.292521],[-434.685601,-152.638764],[-432.273154,-167.108029],[-430.465159,-181.682184]];
path5353_20_points = [[-430.465159,-181.683498],[-430.101674,-198.743118],[-430.818231,-215.741474],[-432.604835,-232.629505],[-435.451496,-249.358149],[-439.348220,-265.878343],[-444.285014,-282.141024],[-450.251885,-298.097132],[-457.238842,-313.697604]];
path5353_21_points = [[-457.238842,-313.697604],[-468.639113,-342.226877],[-480.702958,-370.488010]];
path5353_22_points = [[-506.993336,-441.954192],[-501.102181,-423.846491],[-494.754442,-405.893944],[-487.953556,-388.104808],[-480.702958,-370.487340]];
path5353_23_points = [[-524.202343,-512.003328],[-520.743489,-494.295256],[-516.720252,-476.708947],[-512.135808,-459.257705],[-506.993336,-441.954835]];
path5353_24_points = [[-517.498347,-635.971352],[-520.922213,-620.703407],[-523.610097,-605.318344],[-525.560603,-589.842118],[-526.772337,-574.300685],[-527.243904,-558.720001],[-526.973910,-543.126022],[-525.960959,-527.544704],[-524.203657,-512.002001]];
path5353_25_points = [[-478.294186,-710.270929],[-485.120893,-702.090254],[-491.423711,-693.543079],[-497.189417,-684.654543],[-502.404783,-675.449786],[-507.056585,-665.953949],[-511.131597,-656.192170],[-514.616593,-646.189592],[-517.498347,-635.971352]];
path5353_26_points = [[-454.868692,-729.202399],[-461.132848,-724.978680],[-467.135009,-720.407559],[-472.860386,-715.500991],[-478.294186,-710.270929]];
path5353_27_points = [[-342.452751,-754.276528],[-349.812296,-754.903018],[-357.169505,-755.227625],[-371.840789,-754.979250],[-386.394347,-753.547516],[-400.757921,-750.948535],[-414.859254,-747.198420],[-428.626091,-742.313284],[-441.986174,-736.309239],[-448.491103,-732.892662],[-454.867247,-729.202399]];
path5353_28_points = [[-262.119618,-736.766031],[-271.874971,-740.103665],[-281.728749,-743.116636],[-291.672640,-745.803159],[-301.698327,-748.161446],[-311.797497,-750.189713],[-321.961834,-751.886173],[-332.183023,-753.249040],[-342.452751,-754.276528]];
path5353_29_points = [[-262.118304,-736.767345],[-255.174530,-734.053201],[-248.547483,-731.149184],[-236.171327,-724.843489],[-224.845344,-717.994172],[-214.425041,-710.745147],[-204.765925,-703.240326],[-195.723505,-695.623625],[-178.910780,-680.630229],[-170.851490,-673.541363],[-162.830924,-666.916269],[-154.704591,-660.898860],[-146.327998,-655.633049],[-137.556652,-651.262751],[-132.977793,-649.458392],[-128.246061,-647.931878],[-123.343394,-646.701199],[-118.251732,-645.784344],[-112.953012,-645.199302],[-107.429172,-644.964063],[13.208202,-644.964063],[77.082179,-644.964063],[77.320197,-634.486266],[78.019436,-624.361856],[79.157676,-614.589381],[80.712698,-605.167390],[82.662281,-596.094431],[84.984204,-587.369052],[87.656248,-578.989803],[90.656192,-570.955231],[93.961815,-563.263885],[97.550899,-555.914314],[101.401222,-548.905067],[105.490564,-542.234691],[109.796705,-535.901736],[114.297425,-529.904750],[118.970503,-524.242281],[123.793720,-518.912878],[128.744854,-513.915089],[133.801687,-509.247464],[144.143564,-500.896896],[154.641589,-493.849562],[165.118000,-488.093852],[175.395035,-483.618152],[185.294933,-480.410852],[194.639931,-478.460340],[203.252267,-477.755003],[211.467846,-478.019691],[218.977927,-478.954548],[225.986509,-480.441340],[232.697590,-482.361832]];
path5353_30_points = [[232.697590,-482.361307],[241.146024,-485.372955],[249.318040,-488.970427],[257.184461,-493.133973],[264.716110,-497.843848],[271.883808,-503.080304],[278.658379,-508.823593],[285.010644,-515.053968],[290.911426,-521.751683]];
path5353_31_points = [[490.586246,-398.989030],[498.122247,-420.071664],[504.893980,-441.406714]];
path5353_32_points = [[463.819394,-332.458151],[477.565003,-365.580639],[490.586246,-398.989030]];
path5353_33_points = [[397.442979,711.793942],[410.294081,706.329235],[422.853533,700.255389],[435.099104,693.583685],[447.008565,686.325405]];
path5353_34_points = [[-165.156419,752.373268],[-162.051657,752.511336]];
path5353_35_points = [[321.585701,734.596092],[334.800055,731.830129]];
path5353_36_points = [[-360.037997,724.889539],[-347.721616,728.417414],[-335.296191,731.534090],[-322.772239,734.237153],[-310.160279,736.524187]];
path5353_37_points = [[-428.013692,697.736070],[-419.219197,702.359518],[-410.193559,706.524621]];

module poly_path5353(h, w, res=4)  {
  scale([profile_scale, -profile_scale, 1])
  union()  {
    for (t = [0: len(path5353_0_points)-2]) {
      hull() {
        translate(path5353_0_points[t]) 
          cylinder(h=h, r=w/2, $fn=res);
        translate(path5353_0_points[t + 1]) 
          cylinder(h=h, r=w/2, $fn=res);
      }
    }
    for (t = [0: len(path5353_1_points)-2]) {
      hull() {
        translate(path5353_1_points[t]) 
          cylinder(h=h, r=w/2, $fn=res);
        translate(path5353_1_points[t + 1]) 
          cylinder(h=h, r=w/2, $fn=res);
      }
    }
    for (t = [0: len(path5353_2_points)-2]) {
      hull() {
        translate(path5353_2_points[t]) 
          cylinder(h=h, r=w/2, $fn=res);
        translate(path5353_2_points[t + 1]) 
          cylinder(h=h, r=w/2, $fn=res);
      }
    }
    for (t = [0: len(path5353_3_points)-2]) {
      hull() {
        translate(path5353_3_points[t]) 
          cylinder(h=h, r=w/2, $fn=res);
        translate(path5353_3_points[t + 1]) 
          cylinder(h=h, r=w/2, $fn=res);
      }
    }
    for (t = [0: len(path5353_4_points)-2]) {
      hull() {
        translate(path5353_4_points[t]) 
          cylinder(h=h, r=w/2, $fn=res);
        translate(path5353_4_points[t + 1]) 
          cylinder(h=h, r=w/2, $fn=res);
      }
    }
    for (t = [0: len(path5353_5_points)-2]) {
      hull() {
        translate(path5353_5_points[t]) 
          cylinder(h=h, r=w/2, $fn=res);
        translate(path5353_5_points[t + 1]) 
          cylinder(h=h, r=w/2, $fn=res);
      }
    }
    for (t = [0: len(path5353_6_points)-2]) {
      hull() {
        translate(path5353_6_points[t]) 
          cylinder(h=h, r=w/2, $fn=res);
        translate(path5353_6_points[t + 1]) 
          cylinder(h=h, r=w/2, $fn=res);
      }
    }
    for (t = [0: len(path5353_7_points)-2]) {
      hull() {
        translate(path5353_7_points[t]) 
          cylinder(h=h, r=w/2, $fn=res);
        translate(path5353_7_points[t + 1]) 
          cylinder(h=h, r=w/2, $fn=res);
      }
    }
    for (t = [0: len(path5353_8_points)-2]) {
      hull() {
        translate(path5353_8_points[t]) 
          cylinder(h=h, r=w/2, $fn=res);
        translate(path5353_8_points[t + 1]) 
          cylinder(h=h, r=w/2, $fn=res);
      }
    }
    for (t = [0: len(path5353_9_points)-2]) {
      hull() {
        translate(path5353_9_points[t]) 
          cylinder(h=h, r=w/2, $fn=res);
        translate(path5353_9_points[t + 1]) 
          cylinder(h=h, r=w/2, $fn=res);
      }
    }
    for (t = [0: len(path5353_10_points)-2]) {
      hull() {
        translate(path5353_10_points[t]) 
          cylinder(h=h, r=w/2, $fn=res);
        translate(path5353_10_points[t + 1]) 
          cylinder(h=h, r=w/2, $fn=res);
      }
    }
    for (t = [0: len(path5353_11_points)-2]) {
      hull() {
        translate(path5353_11_points[t]) 
          cylinder(h=h, r=w/2, $fn=res);
        translate(path5353_11_points[t + 1]) 
          cylinder(h=h, r=w/2, $fn=res);
      }
    }
    for (t = [0: len(path5353_12_points)-2]) {
      hull() {
        translate(path5353_12_points[t]) 
          cylinder(h=h, r=w/2, $fn=res);
        translate(path5353_12_points[t + 1]) 
          cylinder(h=h, r=w/2, $fn=res);
      }
    }
    for (t = [0: len(path5353_13_points)-2]) {
      hull() {
        translate(path5353_13_points[t]) 
          cylinder(h=h, r=w/2, $fn=res);
        translate(path5353_13_points[t + 1]) 
          cylinder(h=h, r=w/2, $fn=res);
      }
    }
    for (t = [0: len(path5353_14_points)-2]) {
      hull() {
        translate(path5353_14_points[t]) 
          cylinder(h=h, r=w/2, $fn=res);
        translate(path5353_14_points[t + 1]) 
          cylinder(h=h, r=w/2, $fn=res);
      }
    }
    for (t = [0: len(path5353_15_points)-2]) {
      hull() {
        translate(path5353_15_points[t]) 
          cylinder(h=h, r=w/2, $fn=res);
        translate(path5353_15_points[t + 1]) 
          cylinder(h=h, r=w/2, $fn=res);
      }
    }
    for (t = [0: len(path5353_16_points)-2]) {
      hull() {
        translate(path5353_16_points[t]) 
          cylinder(h=h, r=w/2, $fn=res);
        translate(path5353_16_points[t + 1]) 
          cylinder(h=h, r=w/2, $fn=res);
      }
    }
    for (t = [0: len(path5353_17_points)-2]) {
      hull() {
        translate(path5353_17_points[t]) 
          cylinder(h=h, r=w/2, $fn=res);
        translate(path5353_17_points[t + 1]) 
          cylinder(h=h, r=w/2, $fn=res);
      }
    }
    for (t = [0: len(path5353_18_points)-2]) {
      hull() {
        translate(path5353_18_points[t]) 
          cylinder(h=h, r=w/2, $fn=res);
        translate(path5353_18_points[t + 1]) 
          cylinder(h=h, r=w/2, $fn=res);
      }
    }
    for (t = [0: len(path5353_19_points)-2]) {
      hull() {
        translate(path5353_19_points[t]) 
          cylinder(h=h, r=w/2, $fn=res);
        translate(path5353_19_points[t + 1]) 
          cylinder(h=h, r=w/2, $fn=res);
      }
    }
    for (t = [0: len(path5353_20_points)-2]) {
      hull() {
        translate(path5353_20_points[t]) 
          cylinder(h=h, r=w/2, $fn=res);
        translate(path5353_20_points[t + 1]) 
          cylinder(h=h, r=w/2, $fn=res);
      }
    }
    for (t = [0: len(path5353_21_points)-2]) {
      hull() {
        translate(path5353_21_points[t]) 
          cylinder(h=h, r=w/2, $fn=res);
        translate(path5353_21_points[t + 1]) 
          cylinder(h=h, r=w/2, $fn=res);
      }
    }
    for (t = [0: len(path5353_22_points)-2]) {
      hull() {
        translate(path5353_22_points[t]) 
          cylinder(h=h, r=w/2, $fn=res);
        translate(path5353_22_points[t + 1]) 
          cylinder(h=h, r=w/2, $fn=res);
      }
    }
    for (t = [0: len(path5353_23_points)-2]) {
      hull() {
        translate(path5353_23_points[t]) 
          cylinder(h=h, r=w/2, $fn=res);
        translate(path5353_23_points[t + 1]) 
          cylinder(h=h, r=w/2, $fn=res);
      }
    }
    for (t = [0: len(path5353_24_points)-2]) {
      hull() {
        translate(path5353_24_points[t]) 
          cylinder(h=h, r=w/2, $fn=res);
        translate(path5353_24_points[t + 1]) 
          cylinder(h=h, r=w/2, $fn=res);
      }
    }
    for (t = [0: len(path5353_25_points)-2]) {
      hull() {
        translate(path5353_25_points[t]) 
          cylinder(h=h, r=w/2, $fn=res);
        translate(path5353_25_points[t + 1]) 
          cylinder(h=h, r=w/2, $fn=res);
      }
    }
    for (t = [0: len(path5353_26_points)-2]) {
      hull() {
        translate(path5353_26_points[t]) 
          cylinder(h=h, r=w/2, $fn=res);
        translate(path5353_26_points[t + 1]) 
          cylinder(h=h, r=w/2, $fn=res);
      }
    }
    for (t = [0: len(path5353_27_points)-2]) {
      hull() {
        translate(path5353_27_points[t]) 
          cylinder(h=h, r=w/2, $fn=res);
        translate(path5353_27_points[t + 1]) 
          cylinder(h=h, r=w/2, $fn=res);
      }
    }
    for (t = [0: len(path5353_28_points)-2]) {
      hull() {
        translate(path5353_28_points[t]) 
          cylinder(h=h, r=w/2, $fn=res);
        translate(path5353_28_points[t + 1]) 
          cylinder(h=h, r=w/2, $fn=res);
      }
    }
    for (t = [0: len(path5353_29_points)-2]) {
      hull() {
        translate(path5353_29_points[t]) 
          cylinder(h=h, r=w/2, $fn=res);
        translate(path5353_29_points[t + 1]) 
          cylinder(h=h, r=w/2, $fn=res);
      }
    }
    for (t = [0: len(path5353_30_points)-2]) {
      hull() {
        translate(path5353_30_points[t]) 
          cylinder(h=h, r=w/2, $fn=res);
        translate(path5353_30_points[t + 1]) 
          cylinder(h=h, r=w/2, $fn=res);
      }
    }
    for (t = [0: len(path5353_31_points)-2]) {
      hull() {
        translate(path5353_31_points[t]) 
          cylinder(h=h, r=w/2, $fn=res);
        translate(path5353_31_points[t + 1]) 
          cylinder(h=h, r=w/2, $fn=res);
      }
    }
    for (t = [0: len(path5353_32_points)-2]) {
      hull() {
        translate(path5353_32_points[t]) 
          cylinder(h=h, r=w/2, $fn=res);
        translate(path5353_32_points[t + 1]) 
          cylinder(h=h, r=w/2, $fn=res);
      }
    }
    for (t = [0: len(path5353_33_points)-2]) {
      hull() {
        translate(path5353_33_points[t]) 
          cylinder(h=h, r=w/2, $fn=res);
        translate(path5353_33_points[t + 1]) 
          cylinder(h=h, r=w/2, $fn=res);
      }
    }
    for (t = [0: len(path5353_34_points)-2]) {
      hull() {
        translate(path5353_34_points[t]) 
          cylinder(h=h, r=w/2, $fn=res);
        translate(path5353_34_points[t + 1]) 
          cylinder(h=h, r=w/2, $fn=res);
      }
    }
    for (t = [0: len(path5353_35_points)-2]) {
      hull() {
        translate(path5353_35_points[t]) 
          cylinder(h=h, r=w/2, $fn=res);
        translate(path5353_35_points[t + 1]) 
          cylinder(h=h, r=w/2, $fn=res);
      }
    }
    for (t = [0: len(path5353_36_points)-2]) {
      hull() {
        translate(path5353_36_points[t]) 
          cylinder(h=h, r=w/2, $fn=res);
        translate(path5353_36_points[t + 1]) 
          cylinder(h=h, r=w/2, $fn=res);
      }
    }
    for (t = [0: len(path5353_37_points)-2]) {
      hull() {
        translate(path5353_37_points[t]) 
          cylinder(h=h, r=w/2, $fn=res);
        translate(path5353_37_points[t + 1]) 
          cylinder(h=h, r=w/2, $fn=res);
      }
    }
  }
}

// The shapes
//poly_path5353(height, width);
