fpiesik/ElektroCaster/mechanics/body/inkbodyTest.scad

 import("file.svg");
