fpiesik/ElektroCaster/software/firmwareCtl/06_midi.ino

void setMidiHandles(){
  usbMIDI.setHandleClock(midiClock);
  usbMIDI.setHandleStart(midiStart);
  usbMIDI.setHandleStop(midiStop);
//  usbMIDI.setHandleNoteOn(rcvNoteOn);
//  usbMIDI.setHandleNoteOff(rcvNoteOff);
  usbMIDI.setHandleControlChange(rcvCC);
  usbMIDI.setHandleNoteOn(rcvNoteOn);  // Put only the name of the function
  usbMIDI.setHandleNoteOff(rcvNoteOff);
}

void sndMidiNote(byte note,byte velocity, byte channel){
  if(velocity>0){
    //usbMIDI.sendNoteOn(note, velocity, channel, 0);
    usbMIDI.sendNoteOn(note, velocity, channel);
  }
  if(velocity==0){
    //usbMIDI.sendNoteOff(note, 0, channel, 0);
    usbMIDI.sendNoteOff(note, velocity, channel);
  }
//    Serial.print("note: ");
//    Serial.print(note);
//    Serial.print(" vel: ");
//    Serial.println(velocity);
}

void sndMidiNotePress(int str, int frt, int chn){
  static int lastNote[nStrings];
  static int lastChn[nStrings];
  //int chn=genSq_chn[genSq_actInst][genSq_actPttns[genSq_actPttnsIdx][genSq_actInst]][str][genSq_strEncFnc_chn];
  if (frt > 0){ 
//    for (int s = 0;s<nStrings;s++){
//      sndMidiNote(lastNote[s],0, lastChn[s]);
//    }
    int note=tuning[str]+frt+12;
    if (lastNote[str]!=0 && note == lastNote[str]) sndMidiNote(lastNote[str],0, lastChn[str]);
    sndMidiNote(note,127, chn);
    delay(1);
    if (lastNote[str]!=0 && note != lastNote[str]) sndMidiNote(lastNote[str],0, lastChn[str]);
    lastNote[str]=note;
    lastChn[str]=chn;
  }    
  if (frt == 0){ 
    if (lastNote[str]!=0) sndMidiNote(lastNote[str],0, lastChn[str]);
    lastNote[str]=0;
  }
}

void sndMidiCC(byte cc, byte val,byte ch){
  //usbMIDI.sendControlChange(cc, val, ch);
  usbMIDI.sendControlChange(cc, val, ch);
}

void sndMidiPC(byte program, byte ch){
  usbMIDI.sendProgramChange(program, ch);
}

void sndMidiClck(int state){
    if(state==0)usbMIDI.sendRealTime(midi::Start);
    if(state==1)usbMIDI.sendRealTime(midi::Clock);
    if(state==2)usbMIDI.sendRealTime(midi::Stop);
}


void rcvNoteOn(byte channel, byte note, byte velocity) {
  extNotes[channel][note]=velocity;
  midiKick(channel,velocity);
  
}

void rcvNoteOff(byte channel, byte note, byte velocity) {
  extNotes[channel][note]=0;
}

void midiClock(){ 
  if(extClk==1 && clckOn==1){
    mClock++;
    cmpClck(mClock);
  }
}

void midiStart() {
  mClock=-1;
  //extClk=1;
  cmpClck(mClock);
}
void midiStop() {
  mClock = -1;
  //extClk = 1;
  cmpClck(mClock);
  for(int ch=0;ch<=16;ch++){
    for(int n=0;n<=127;n++){
      extNotes[ch][n]=0;
    }
  }
  genSq_allNOff();
}

void genSq_allNOff(){
  for(int str = 0; str<nStrings; str++){
    sndMidiNotePress(str, 0, 1); //channel is irrelevant when frt==0
  }
  for(int inst = 0; inst<genSq_nInst; inst++){
    for(int str = 0; str<nStrings; str++){
      for(int pttn = 0; pttn<genSq_nPttn; pttn++){
        genSq_sndStpOffNMW(inst, pttn, str);
      }
    }
  }
}

void midiKick(int chn, int v){
  if(chn<=nStrings){
    int s = nStrings-chn;
    sndTrigEnv(s,v/127.0);
    kick(s);
  }
  
//  for(int s=0;s<nStrings;s++){
//    if(n == tuning[s]){
//    sndTrigEnv(s,v/127.0);
//    kick(s);
//    }
//  }
  
}

void rcvCC(byte ch, byte cc, byte data) {
  ccState[cc]=data;
  //sndCC();
  float val=data/127.0; 
  
//  for(int n=0;n<4;n++){
//    if(cc==ccFilter[n]){
//      valFilter[n]=scale(val,0,sclFilter[n]);
//      chFilter(n,valFilter[n]);
//    }
//  }
//
//  for(int n=0;n<7;n++){
//    if(cc==ccEnvA[n]){
//      float sclVal=scale(val,1,sclEnvA[n]);
//      chEnvA(n,sclVal);
//    }
//    if(cc==ccEnvF[n]){
//      float sclVal=scale(val,1,sclEnvF[n]);
//      chEnvF(n,sclVal);
//    }
//  }
  
  if(cc==10){
    rootNote=ccState[cc]%12;
  }
  if(cc==11){
    if(ccState[cc]%16<nScales)scls_sclSel=ccState[cc]%16;
    scls_sclStp=int(ccState[cc]/16);
  }
  if(cc==12){
    scls_sclStp=ccState[cc]%scls_numSclStp[scls_sclSel];
  }
  if(cc==13){
    sndLfo1(3, val);
  }
  
}
