fpiesik/ElektroCaster/software/firmwareHid/send.ino

#include "ProtocolHid.h"

void sndA(byte idx, int val){
  Serial6.write(idx + nDigital + HID_CMD_BASE);
  delayMicroseconds(waitS);
  Serial6.write(map(val, 0,1023,0,HID_ANALOG_MAX_VALUE));
  delayMicroseconds(waitS);
}

void sndD(byte idx, int val){
  Serial6.write(idx + HID_CMD_BASE);
  delayMicroseconds(waitS);
  Serial6.write(val);
  delayMicroseconds(waitS);
}

void sndR(byte idx, int val){
  Serial6.write(idx + HID_ROTARY_OFFSET + HID_CMD_BASE);
  delayMicroseconds(waitS);
  Serial6.write(val);
  delayMicroseconds(waitS);
}

void sndE(byte idx, int val){
  Serial6.write(idx + HID_ENCODER_OFFSET + HID_CMD_BASE);
  delayMicroseconds(waitS);
  Serial6.write(val);
  delayMicroseconds(waitS);
}

void sndF(){
  Serial6.write(HID_FRAME_END);
}

void sendAll(){
  for(int i=0;i<nDigital;i++){
      sndD(i,dVal[i]);
      lastDVal[i]=dVal[i];
    
  }

  for(int i=0;i<nAnalog;i++){
      if(i!=19&&i!=20&&i!=21){
        sndA(i,aVal[i]);
        lastAVal[i]=aVal[i];
      }
    }

    for(int i=0;i<3;i++){
      lastRsState[i]=rsState[i];
      sndR(i,rsState[i]);
    }
  }


void sendAllNew(){
  for(int i=0;i<nDigital;i++){
    if(dVal[i]!=lastDVal[i]){
      sndD(i,dVal[i]);
      lastDVal[i]=dVal[i];
    }
  }
 
  for(int i=0;i<nAnalog;i++){
    if(aVal[i]>lastAVal[i]+2 || aVal[i]<lastAVal[i]-2){
      if(i!=19&&i!=20&&i!=21){
        sndA(i,aVal[i]);
        lastAVal[i]=aVal[i];
      }
    }
  }

  if(newEnc0 != pos0)sndE(0,newEnc0 - pos0 + 100),pos0 = newEnc0;
  if(newEnc1 != pos1)sndE(1,newEnc1 - pos1 + 100),pos1 = newEnc1;
  if(newEnc2 != pos2)sndE(2,newEnc2 - pos2 + 100),pos2 = newEnc2;
  if(newEnc3 != pos3)sndE(3,newEnc3 - pos3 + 100),pos3 = newEnc3;
  if(newEnc4 != pos4)sndE(4,newEnc4 - pos4 + 100),pos4 = newEnc4;
  if(newEnc5 != pos5)sndE(5,newEnc5 - pos5 + 100),pos5 = newEnc5;
  if(newEnc6 != pos6)sndE(6,newEnc6 - pos6 + 100),pos6 = newEnc6;
  if(newEnc7 != pos7)sndE(7,newEnc7 - pos7 + 100),pos7 = newEnc7;
  
  for(int i=0;i<3;i++){
    if(rsState[i]!=lastRsState[i]){
      lastRsState[i]=rsState[i];
      sndR(i,rsState[i]);
    }
  }

  sndF();
}
